UnbDroid/balancer_race/placas/PDFs/invertida_alimentacao_etch_copper_bottom.pdf

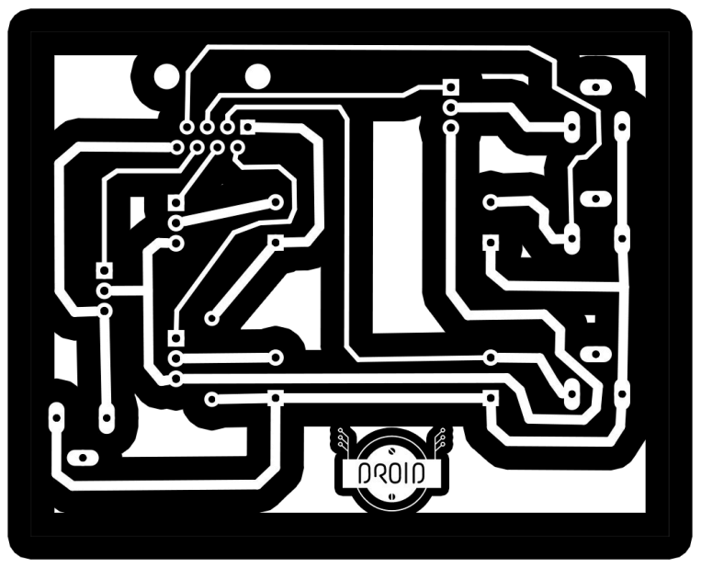
[picture p1: page 1]
