UnbDroid/balancer_race/placas/PDFs/invertida_principal_etch_copper_bottom.pdf

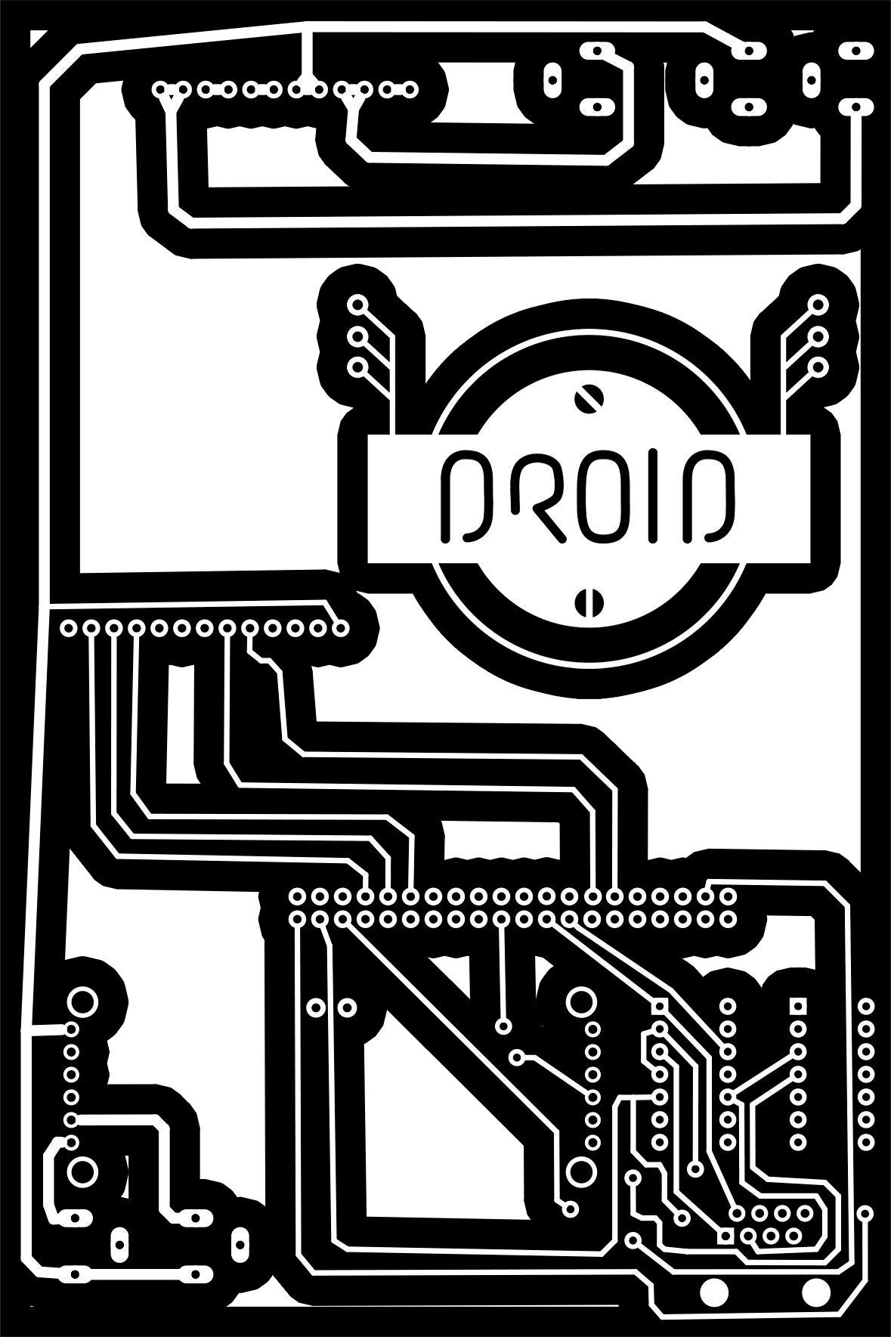
[picture p2: page 1]
