UnbDroid/balancer_race/placas/PDFs/invertida_principal_etch_copper_top.pdf

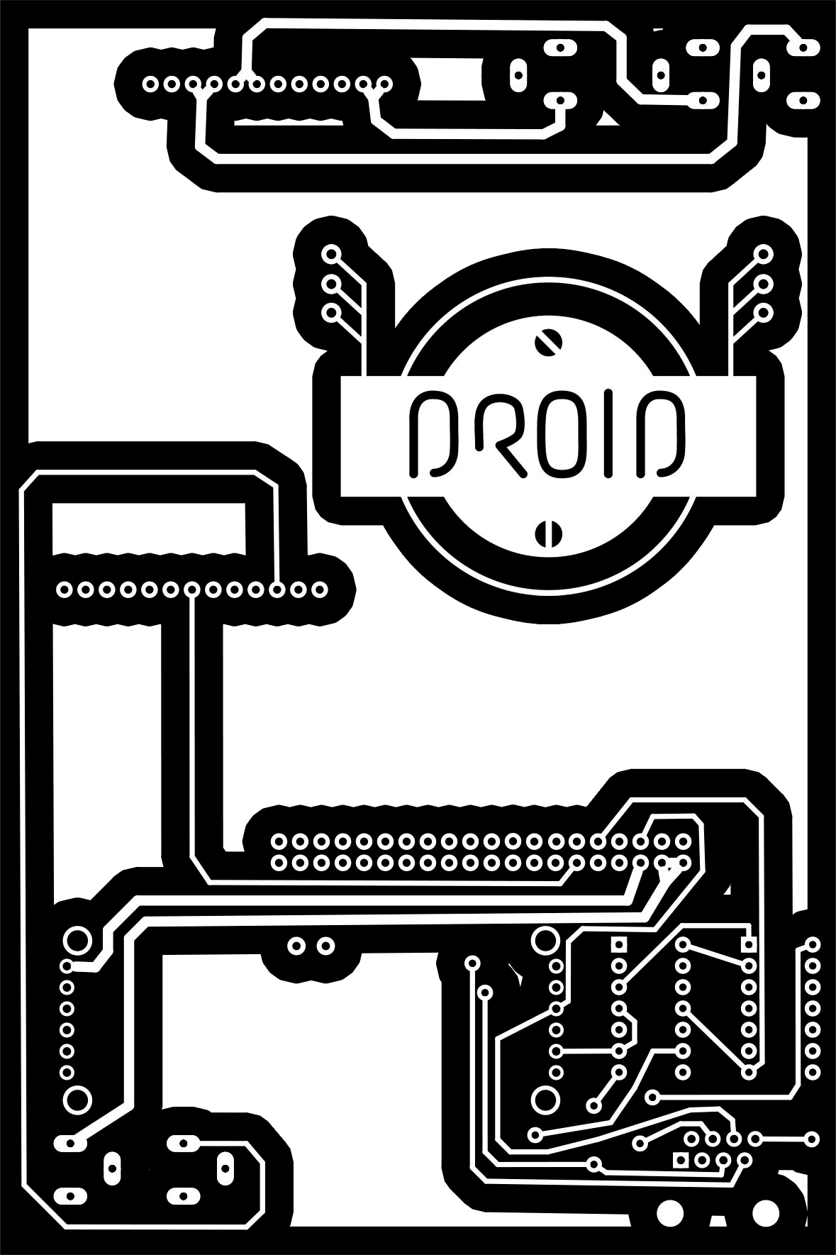
[picture p3: page 1]
