UnbDroid/balancer_race/placas/PDFs/invertidos merge.pdf

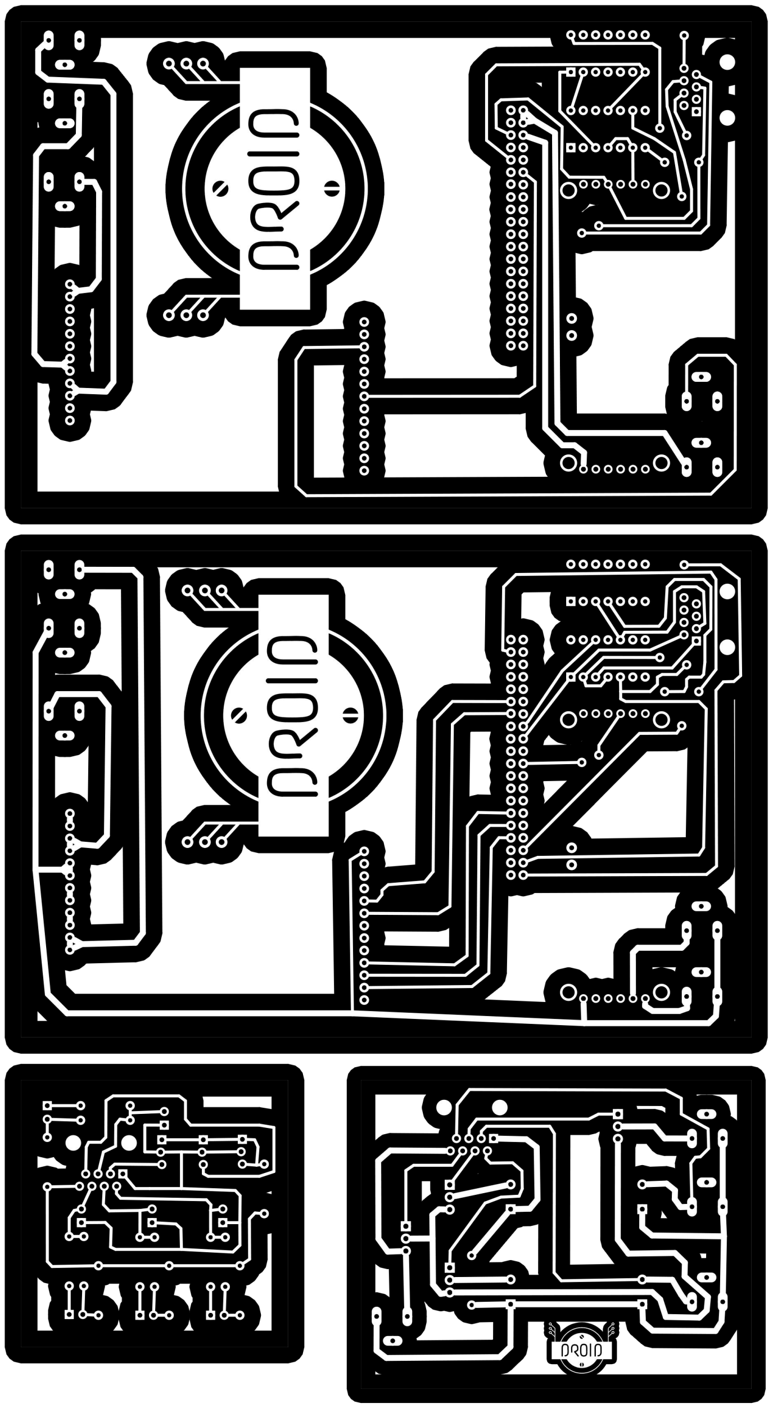
[picture p4: page 1]
