UnbDroid/balancer_race/placas/PDFs/invertida_painel_etch_copper_bottom.pdf

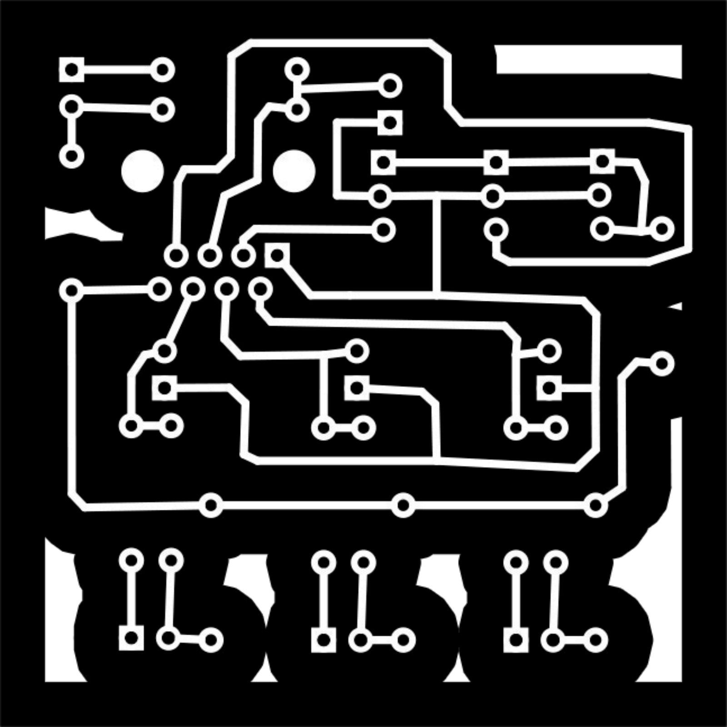
[picture p5: page 1]
