UnbDroid/balancer_race/placas/PDFs/sensores/pronto_para_impressao_sensores_etch_copper_bottom_mirror.pdf

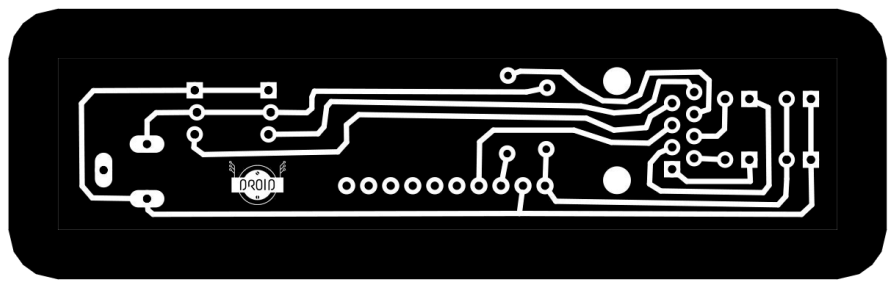
[picture p6: page 1]
