UnbDroid/balancer_race/placas/PDFs/alimentacao2/alimentacao invertida.pdf

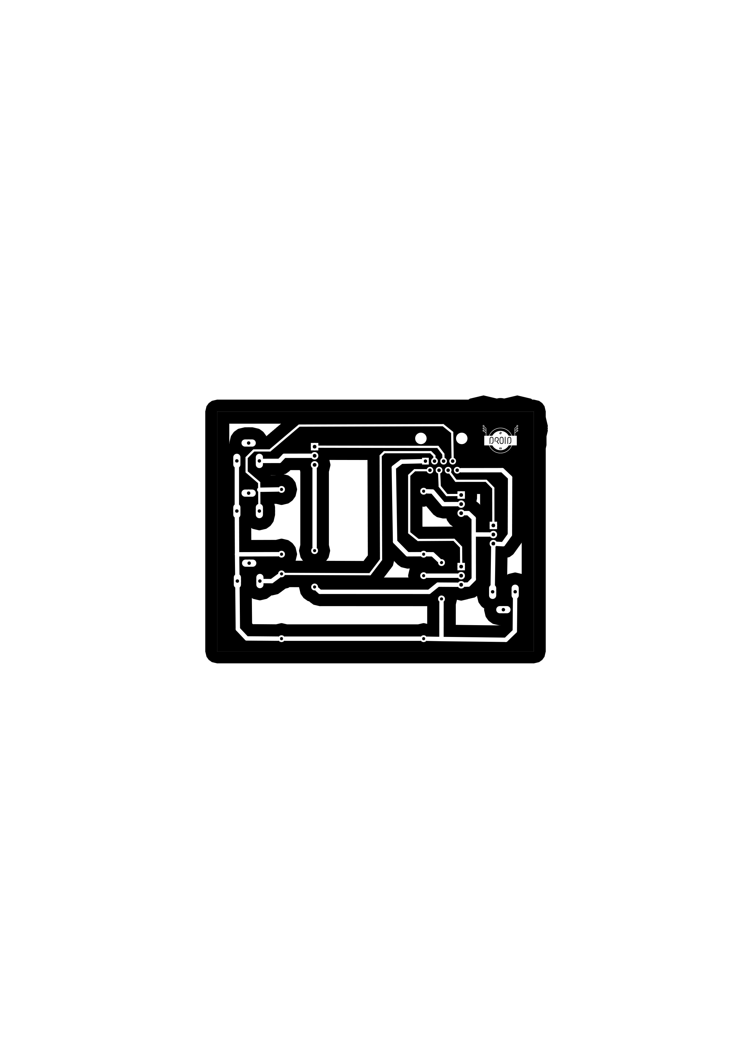
[picture p7: page 1]
