UnbDroid/balancer_race/MATLAB/plots/accel_xyz_static.jpg

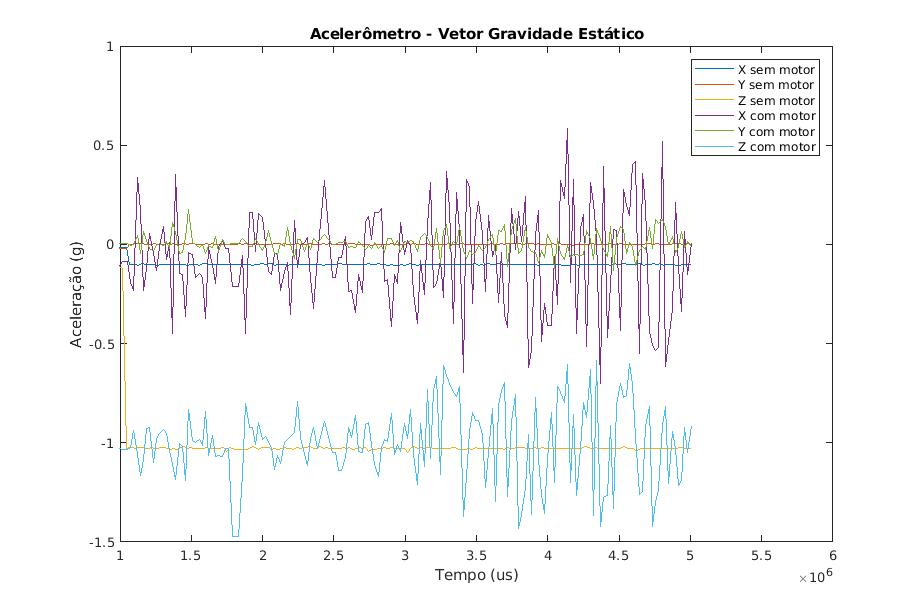
MATLAB/plots/accel_xyz_static.jpg
