UnbDroid/balancer_race/MATLAB/plots/accelXlowfilter.jpg

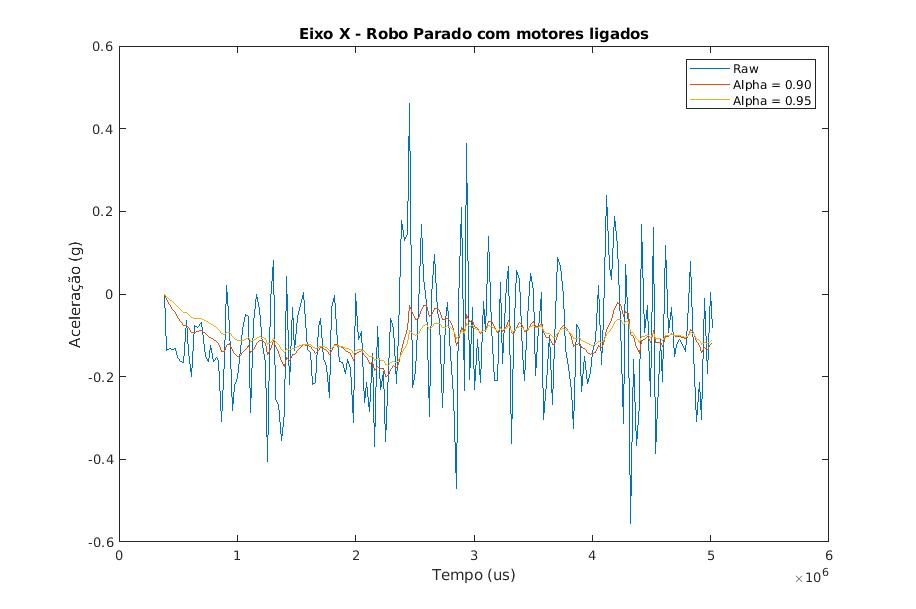
MATLAB/plots/accelXlowfilter.jpg
