UnbDroid/balancer_race/MATLAB/plots/accelYlowfilter.jpg

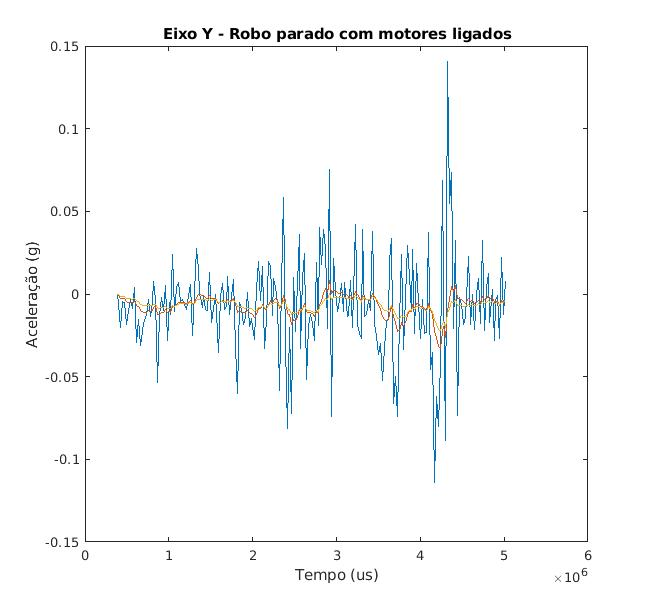
MATLAB/plots/accelYlowfilter.jpg
