UnbDroid/balancer_race/MATLAB/plots/accelZlowfilter.jpg

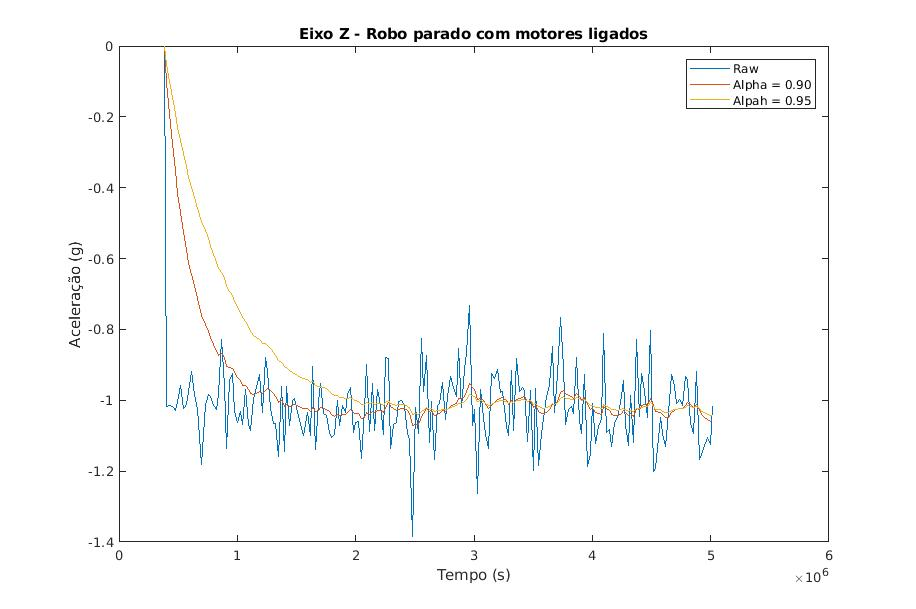
MATLAB/plots/accelZlowfilter.jpg
