UnbDroid/balancer_race/MATLAB/plots/control_gyro_accel_alpha_070.jpg

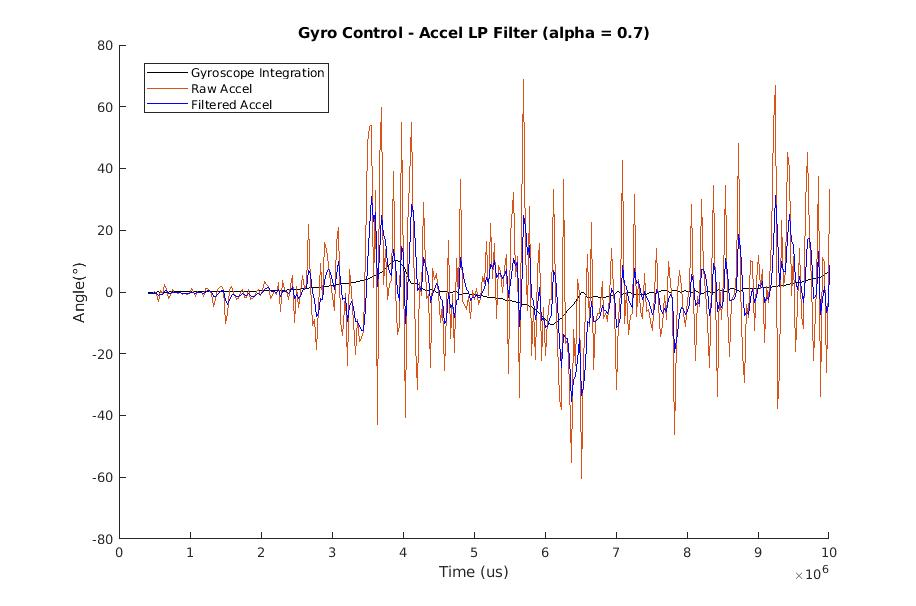
MATLAB/plots/control_gyro_accel_alpha_070.jpg
