UnbDroid/balancer_race/MATLAB/plots/control_gyro_accel_alpha_080.jpg

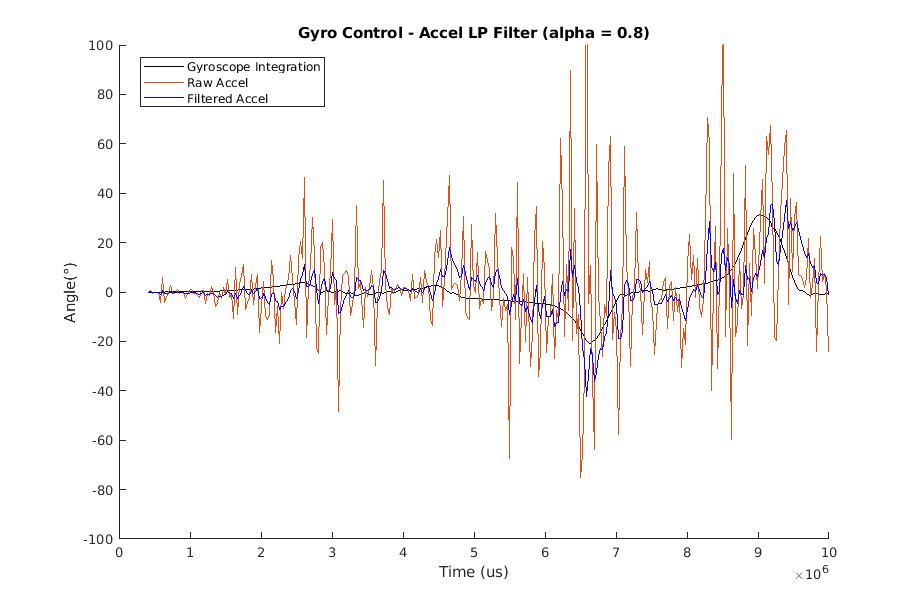
MATLAB/plots/control_gyro_accel_alpha_080.jpg
