UnbDroid/balancer_race/MATLAB/plots/controlandoMotores/endofthedeadzone.jpg

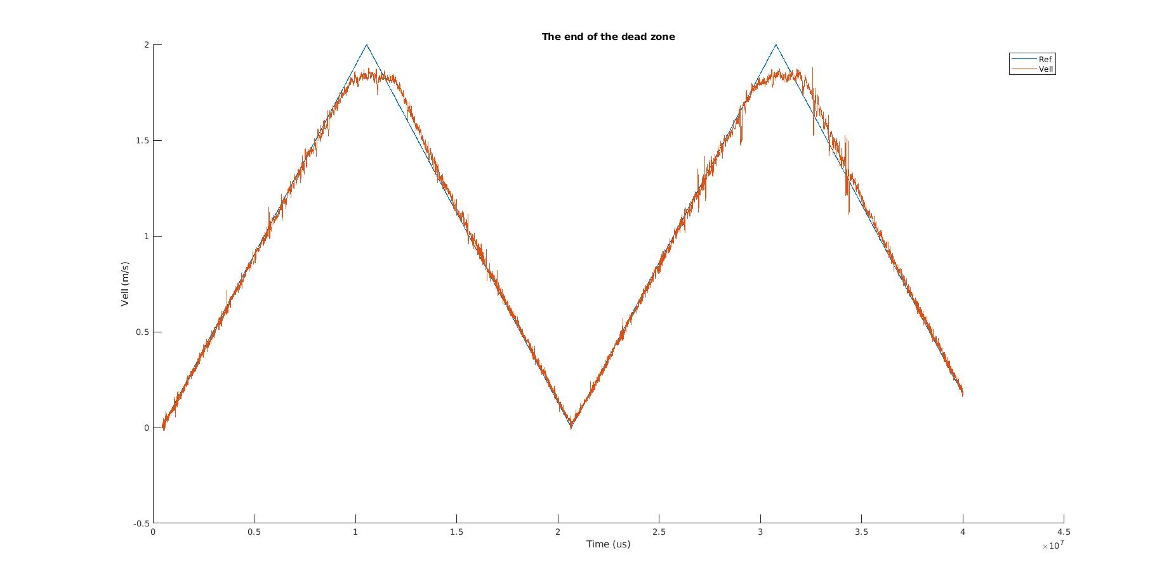
MATLAB/plots/controlandoMotores/endofthedeadzone.jpg
