UnbDroid/balancer_race/MATLAB/plots/controlandoMotores/plot.jpg

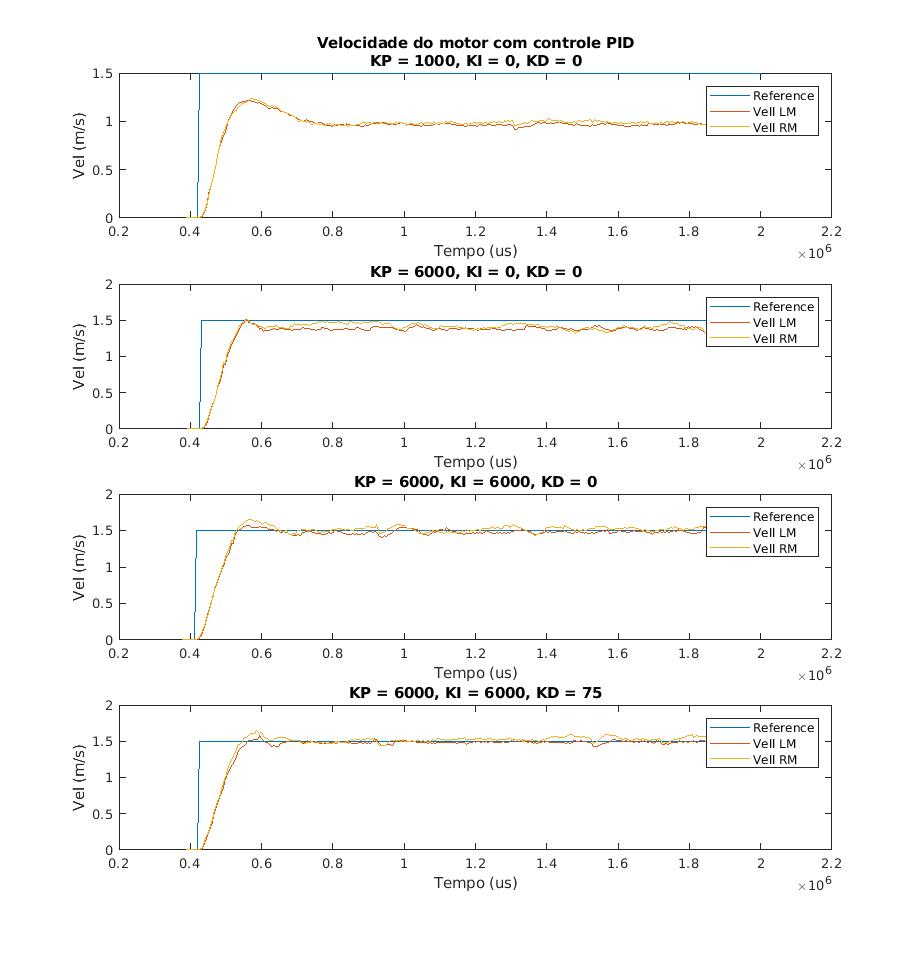
MATLAB/plots/controlandoMotores/plot.jpg
