UnbDroid/balancer_race/MATLAB/plots/filtrandoEncoder/fast.jpg

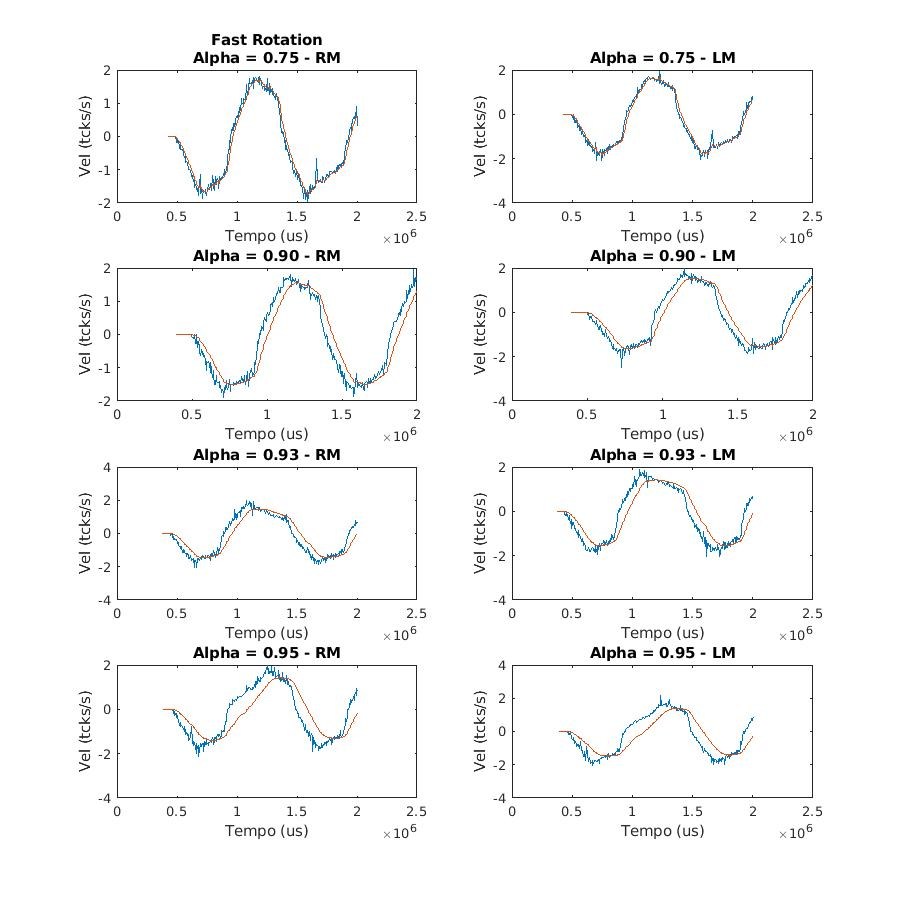
MATLAB/plots/filtrandoEncoder/fast.jpg
