UnbDroid/balancer_race/MATLAB/plots/filtrandoEncoder/slow.jpg

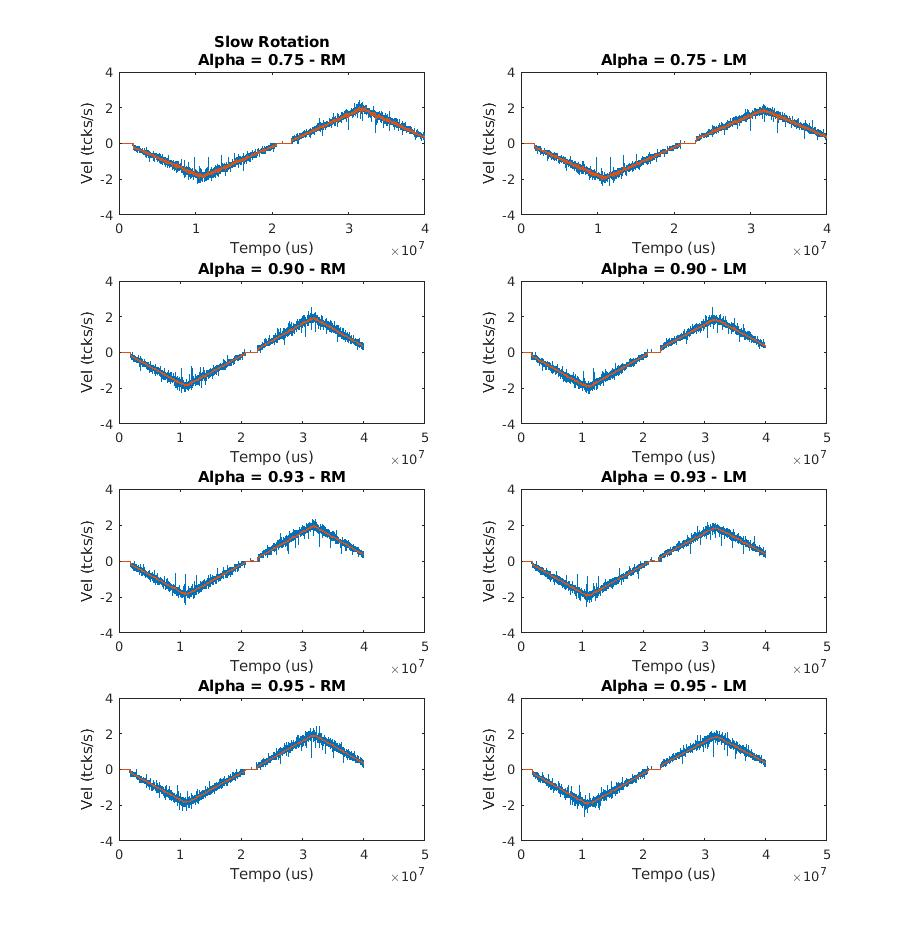
MATLAB/plots/filtrandoEncoder/slow.jpg
