UnbDroid/balancer_race/MATLAB/plots/ligandoeconder/offmottoroffecoder.jpg

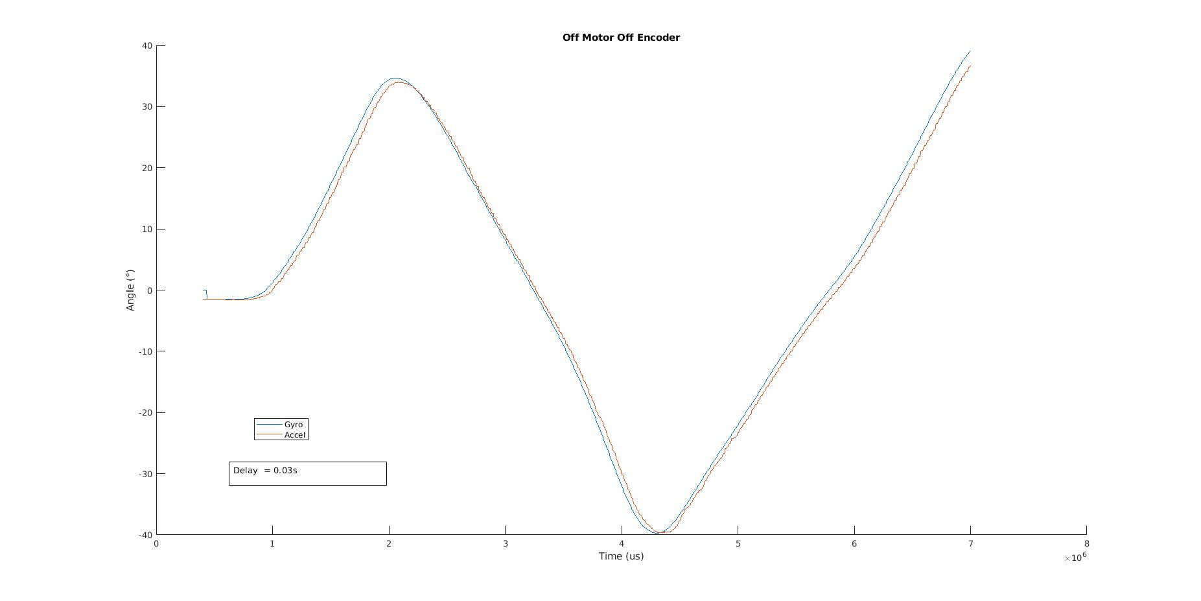
MATLAB/plots/ligandoeconder/offmottoroffecoder.jpg
