UnbDroid/balancer_race/MATLAB/plots/ligandoeconder/onmottoroffecoder.jpg

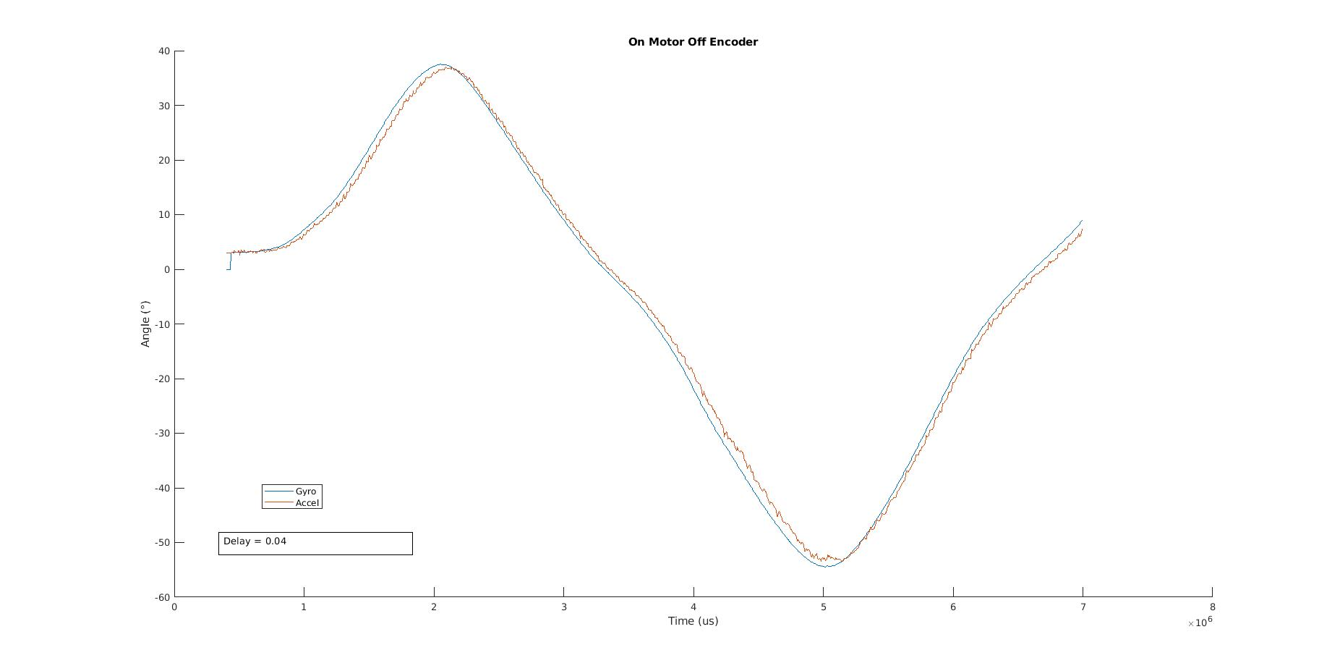
MATLAB/plots/ligandoeconder/onmottoroffecoder.jpg
