UnbDroid/balancer_race/MATLAB/plots/ligandoeconder/onmottoronecoder.jpg

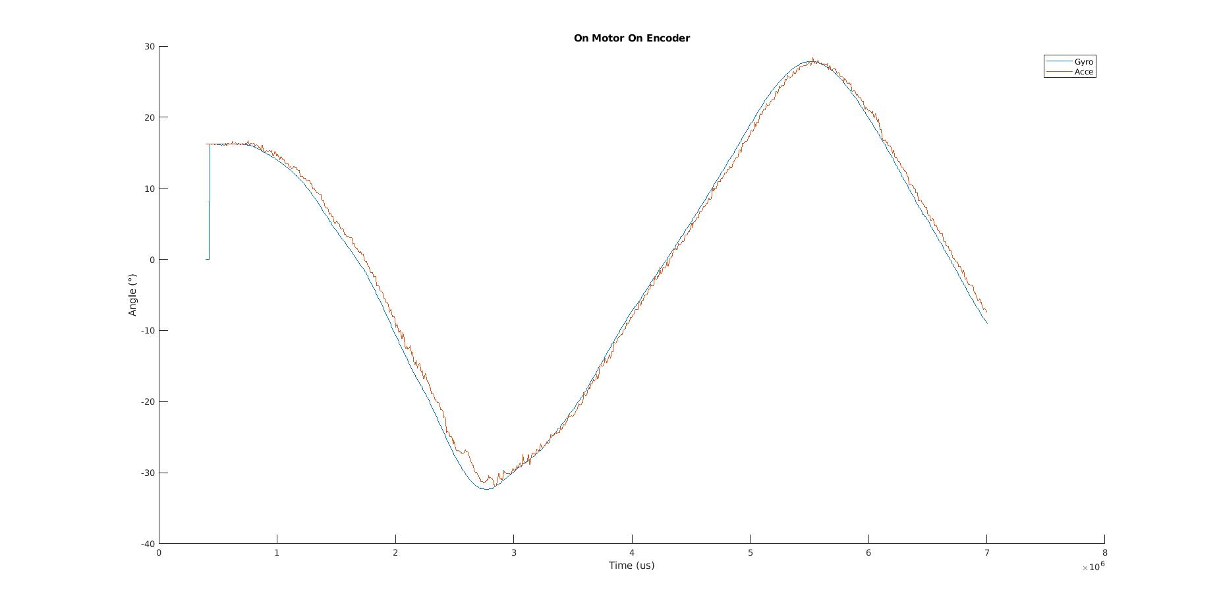
MATLAB/plots/ligandoeconder/onmottoronecoder.jpg
