UnbDroid/balancer_race/MATLAB/plots/motor_rapido/equilibrando.jpg

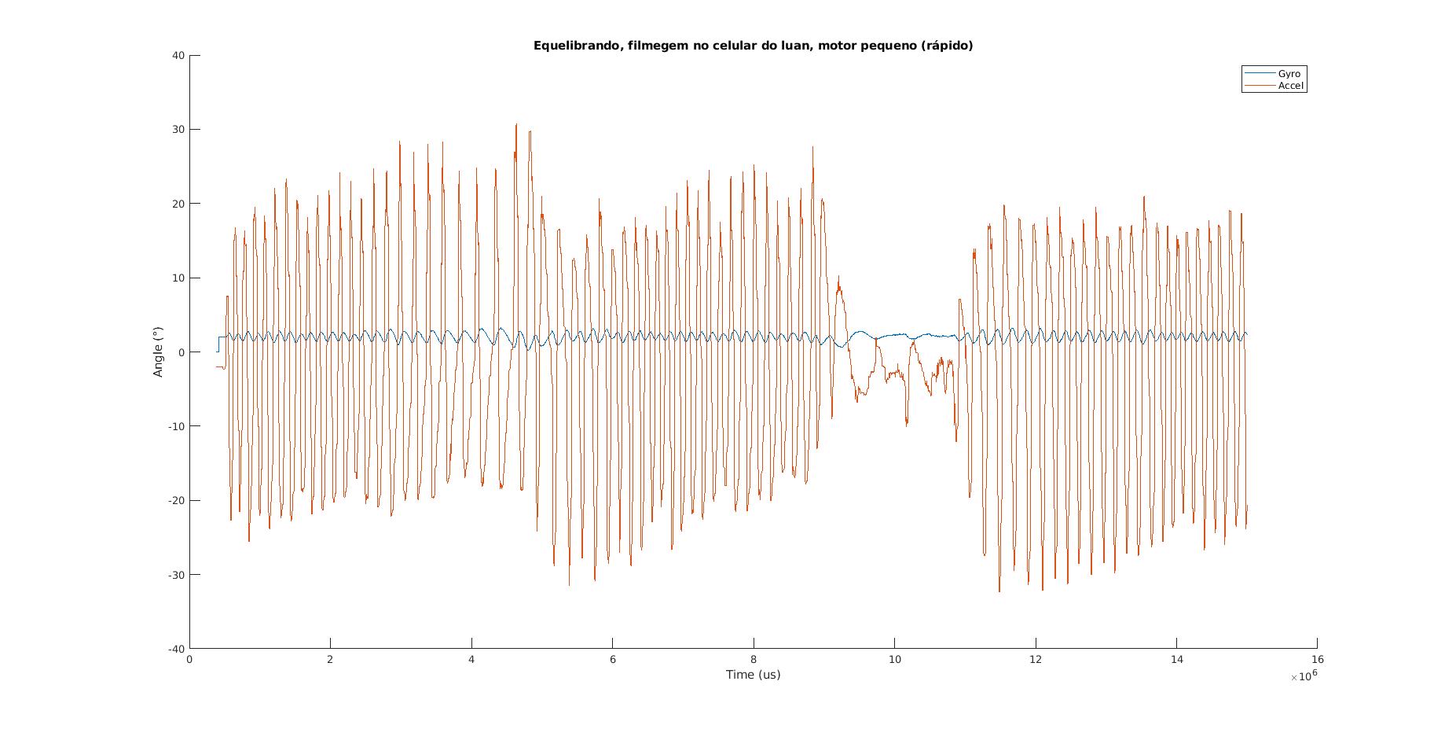
MATLAB/plots/motor_rapido/equilibrando.jpg
