UnbDroid/balancer_race/MATLAB/plots/motor_rapido/offmotor_offencoder.jpg

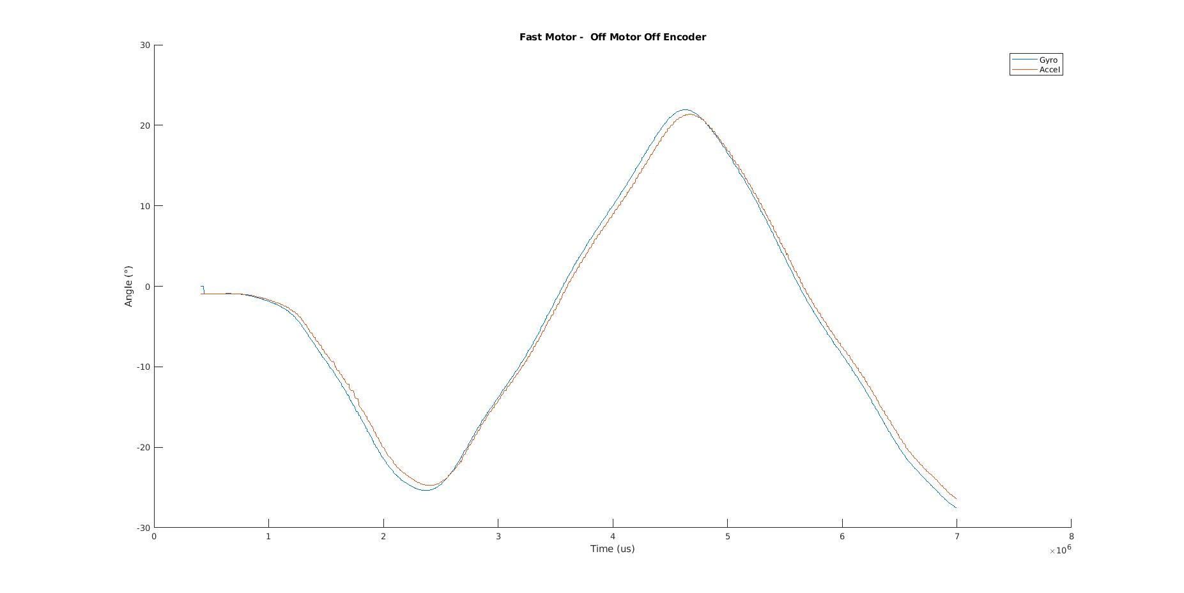
MATLAB/plots/motor_rapido/offmotor_offencoder.jpg
