UnbDroid/balancer_race/MATLAB/plots/motor_rapido/onmotor_offencoder.jpg

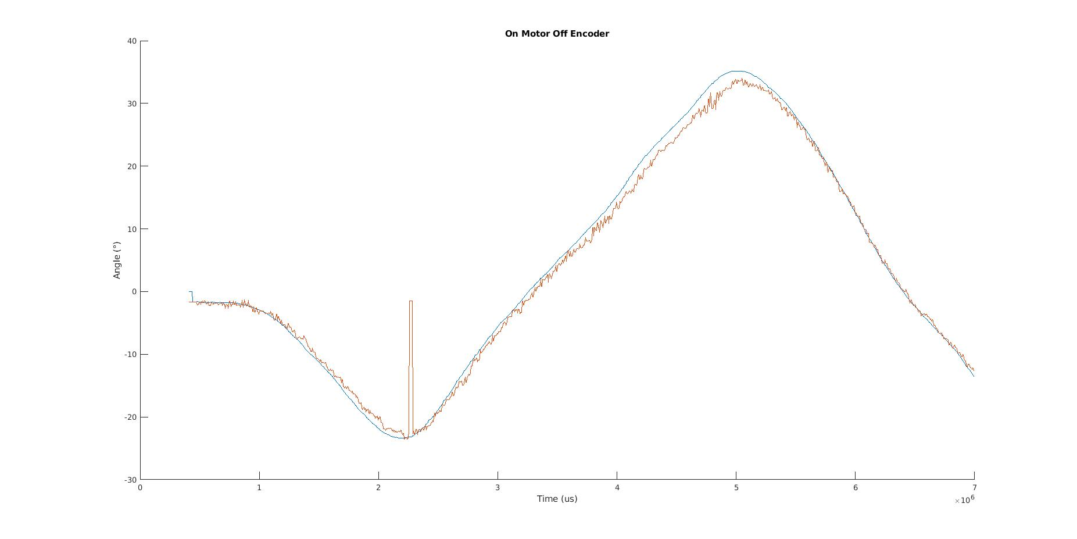
MATLAB/plots/motor_rapido/onmotor_offencoder.jpg
