UnbDroid/balancer_race/MATLAB/plots/motor_rapido/onmotor_onencoder.jpg

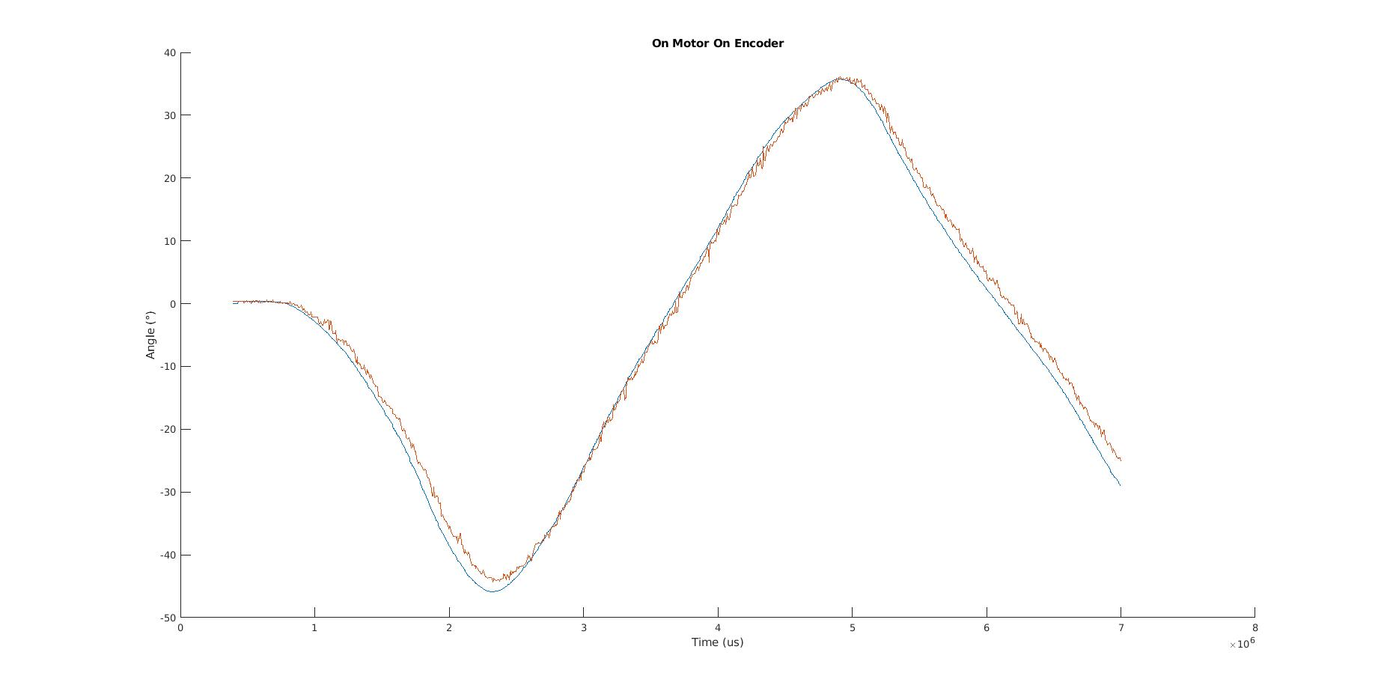
MATLAB/plots/motor_rapido/onmotor_onencoder.jpg
