UnbDroid/balancer_race/MATLAB/plots/mvmda_lowpass/n3a00-offmotor.jpg

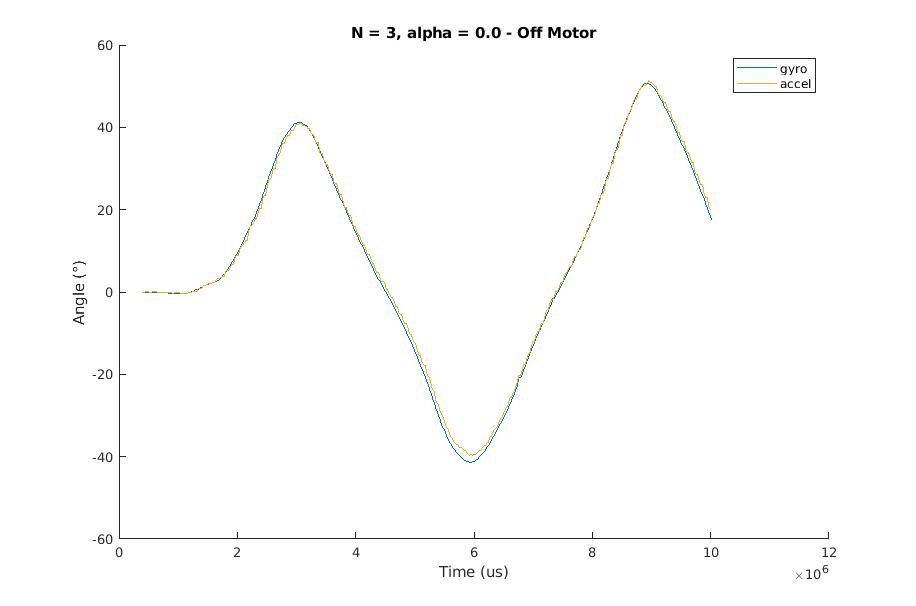
MATLAB/plots/mvmda_lowpass/n3a00-offmotor.jpg
