UnbDroid/balancer_race/MATLAB/plots/mvmda_lowpass/n3a03-offmotor.jpg

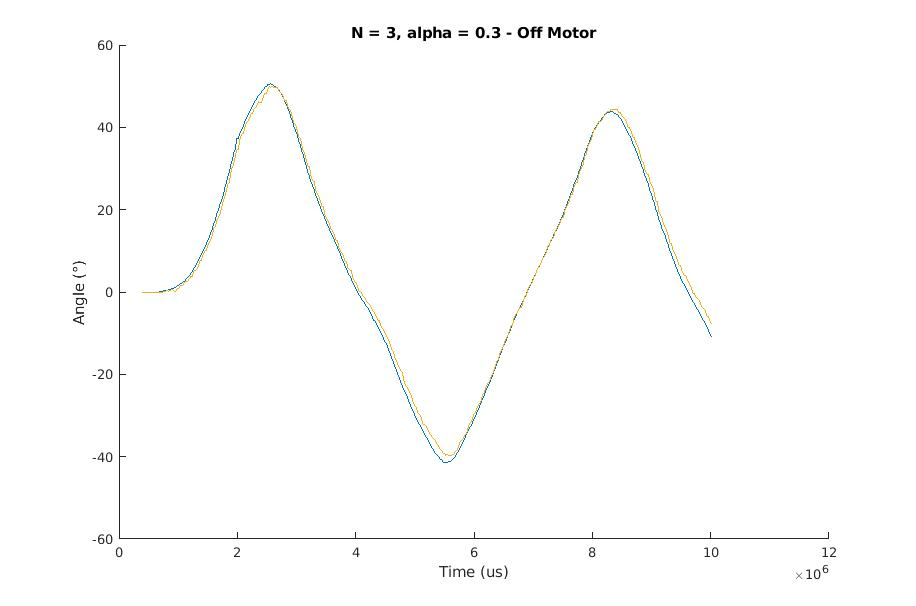
MATLAB/plots/mvmda_lowpass/n3a03-offmotor.jpg
