UnbDroid/balancer_race/MATLAB/plots/mvmda_lowpass/n3a03-onmotor.jpg

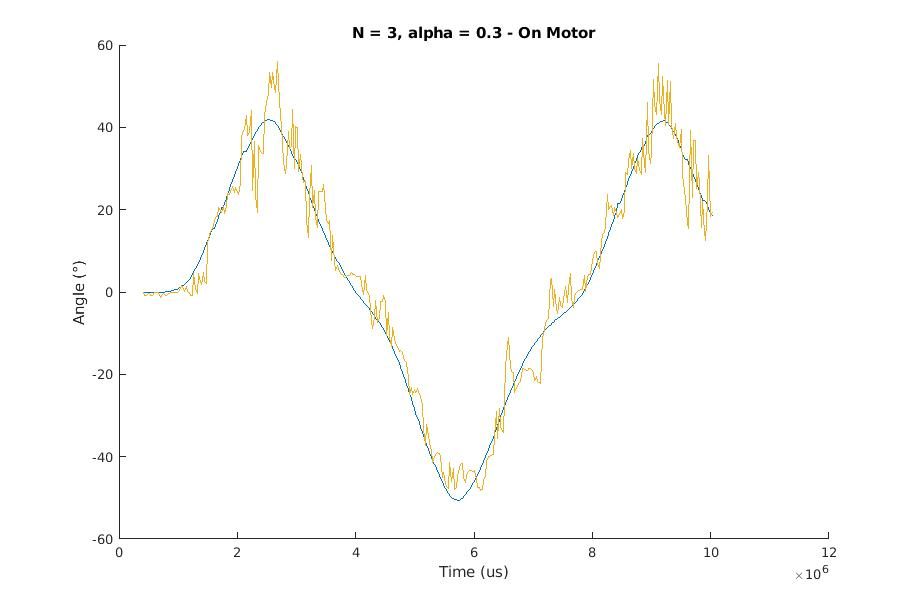
MATLAB/plots/mvmda_lowpass/n3a03-onmotor.jpg
