UnbDroid/balancer_race/MATLAB/plots/mvmda_lowpass/n3a05-offmotor.jpg

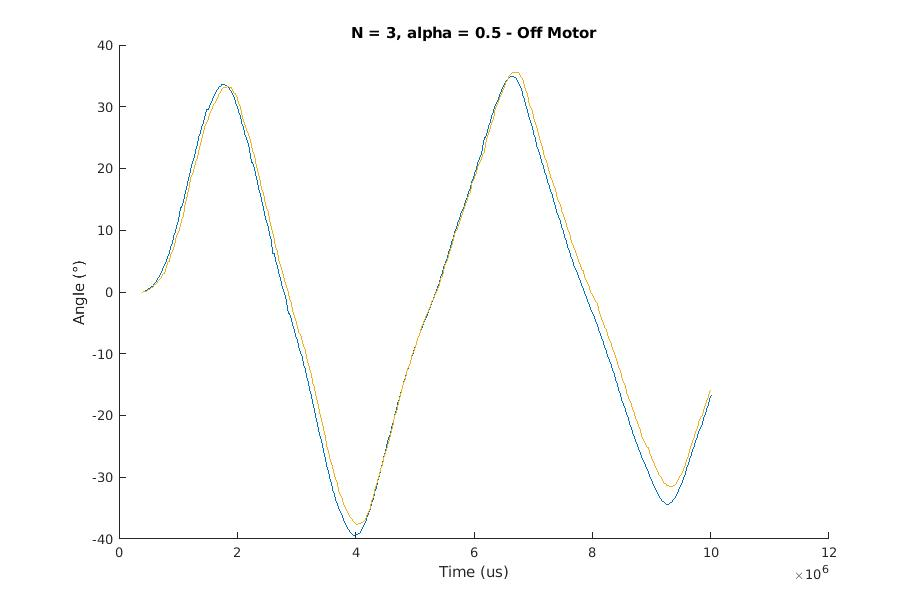
MATLAB/plots/mvmda_lowpass/n3a05-offmotor.jpg
