UnbDroid/balancer_race/MATLAB/plots/mvmda_lowpass/n3a07-offmotor.jpg

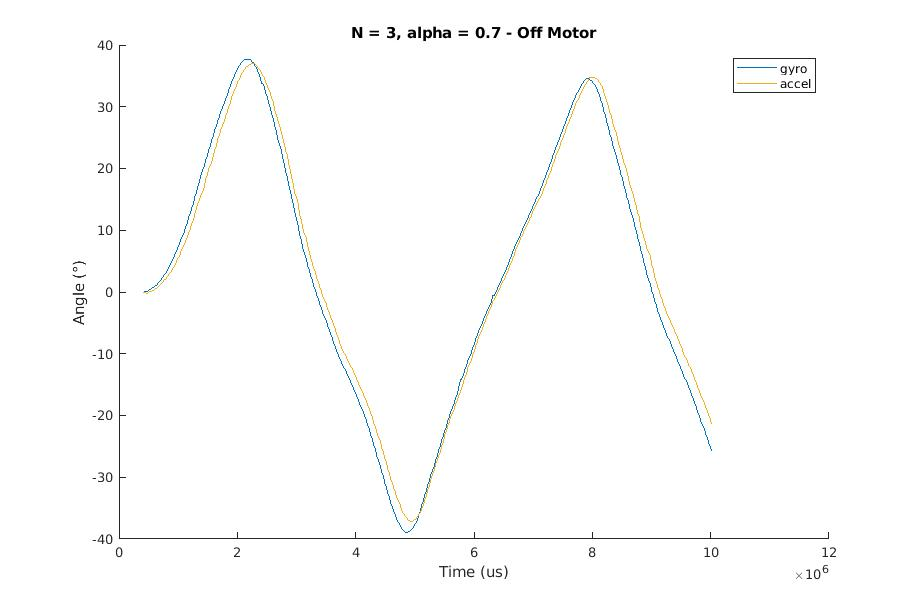
MATLAB/plots/mvmda_lowpass/n3a07-offmotor.jpg
