UnbDroid/balancer_race/MATLAB/plots/mvmda_lowpass/n3a07-onmotor.jpg

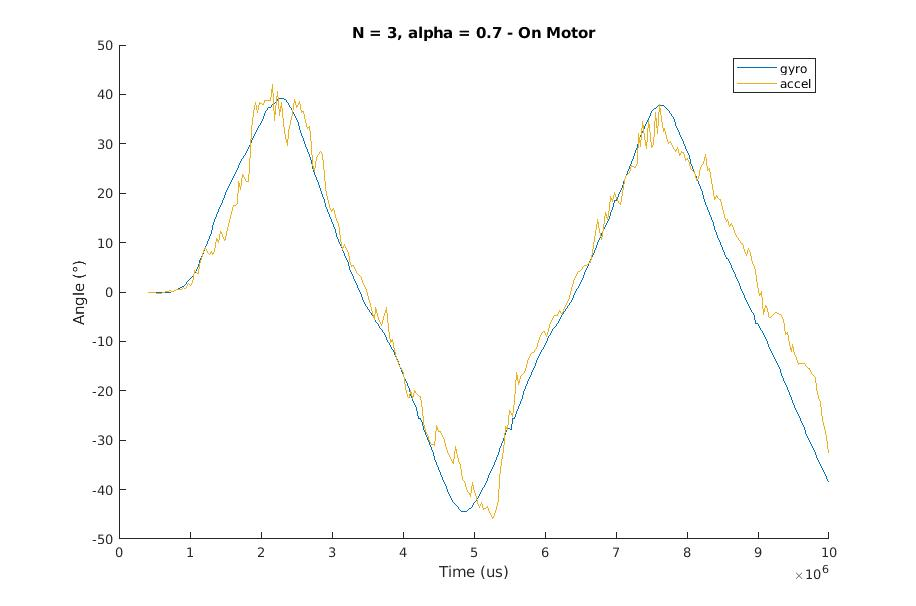
MATLAB/plots/mvmda_lowpass/n3a07-onmotor.jpg
