UnbDroid/balancer_race/MATLAB/plots/mvmda_lowpass/nofilter-offmotor.jpg

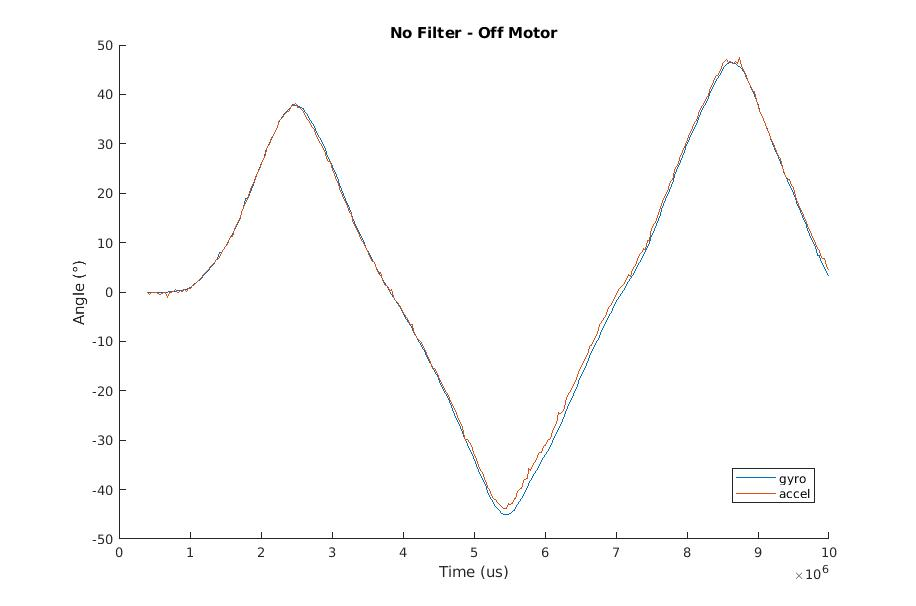
MATLAB/plots/mvmda_lowpass/nofilter-offmotor.jpg
