UnbDroid/balancer_race/MATLAB/plots/mvmda_lowpass/nofilter-onmotor.jpg

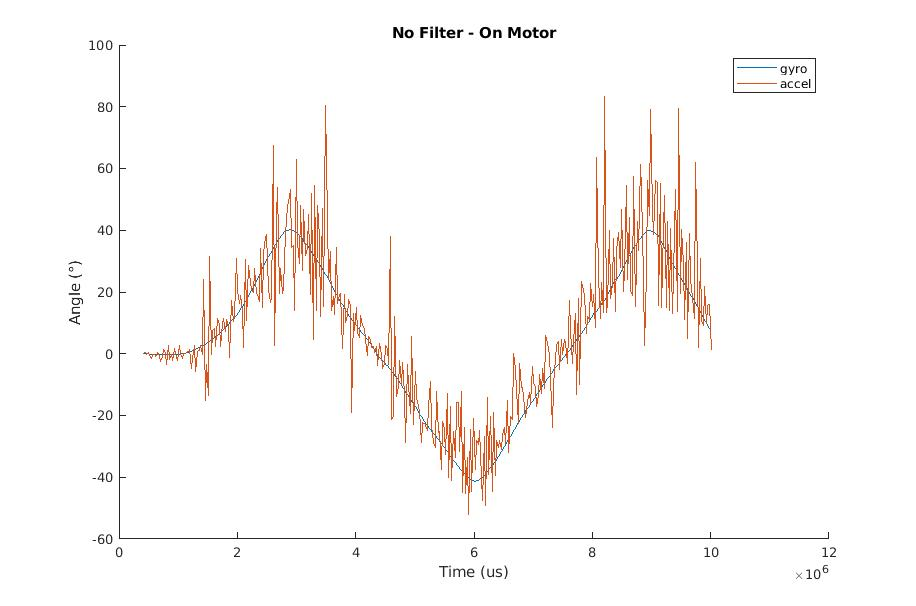
MATLAB/plots/mvmda_lowpass/nofilter-onmotor.jpg
