UnbDroid/balancer_race/MATLAB/plots/EncoderTest/controle/18h30.jpg

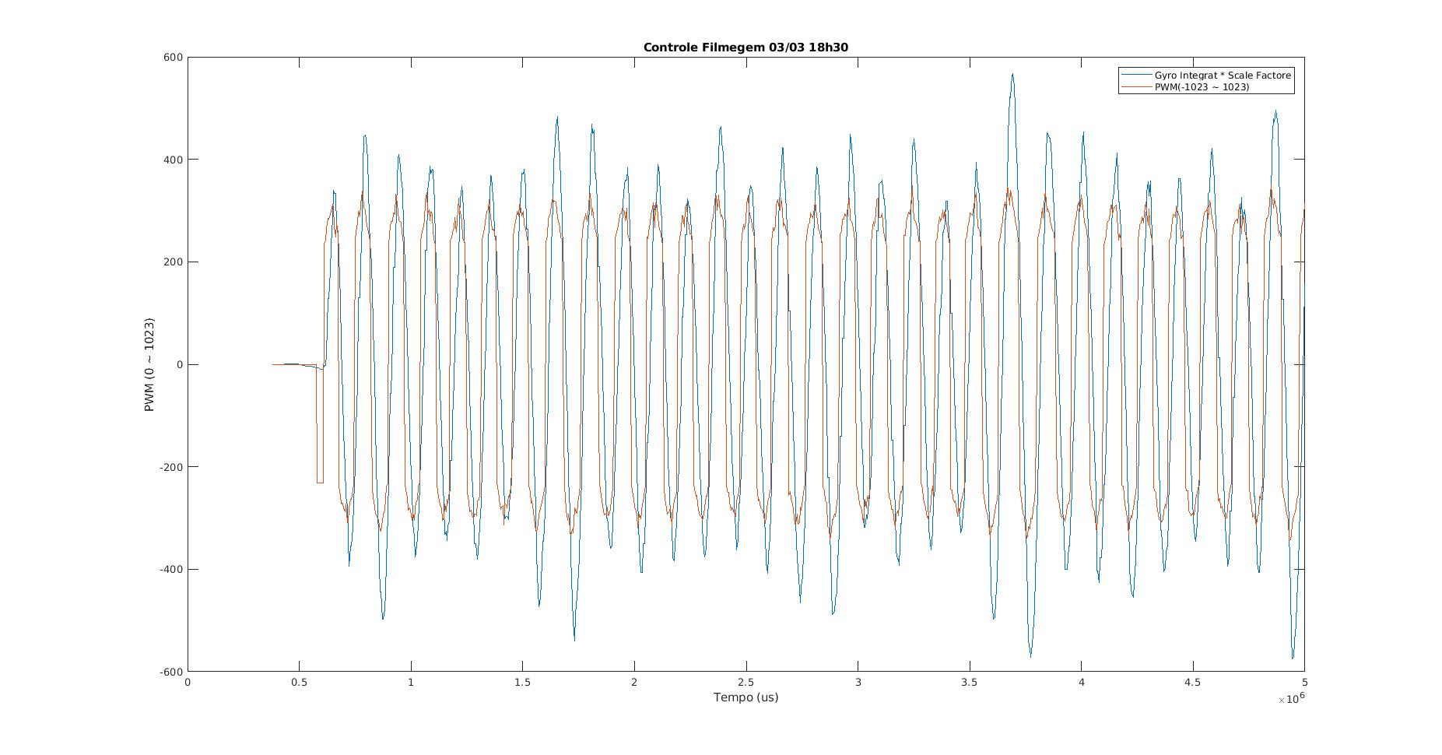
MATLAB/plots/EncoderTest/controle/18h30.jpg
