UnbDroid/balancer_race/MATLAB/plots/EncoderTest/dead_zone/Left Motor - OnFwd - DZ.jpg

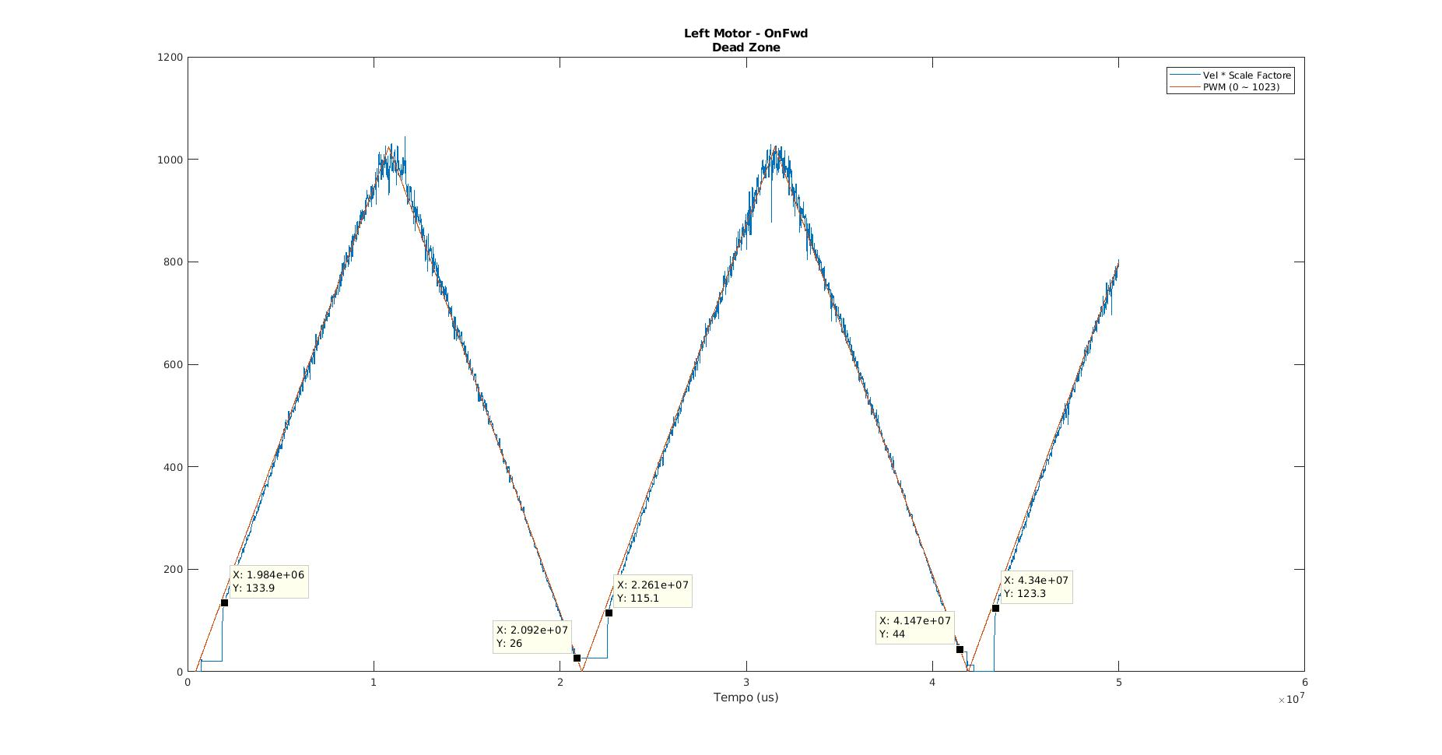
MATLAB/plots/EncoderTest/dead_zone/Left Motor - OnFwd - DZ.jpg
