UnbDroid/balancer_race/MATLAB/plots/EncoderTest/dead_zone/Left Motor - OnFwd - Raw.jpg

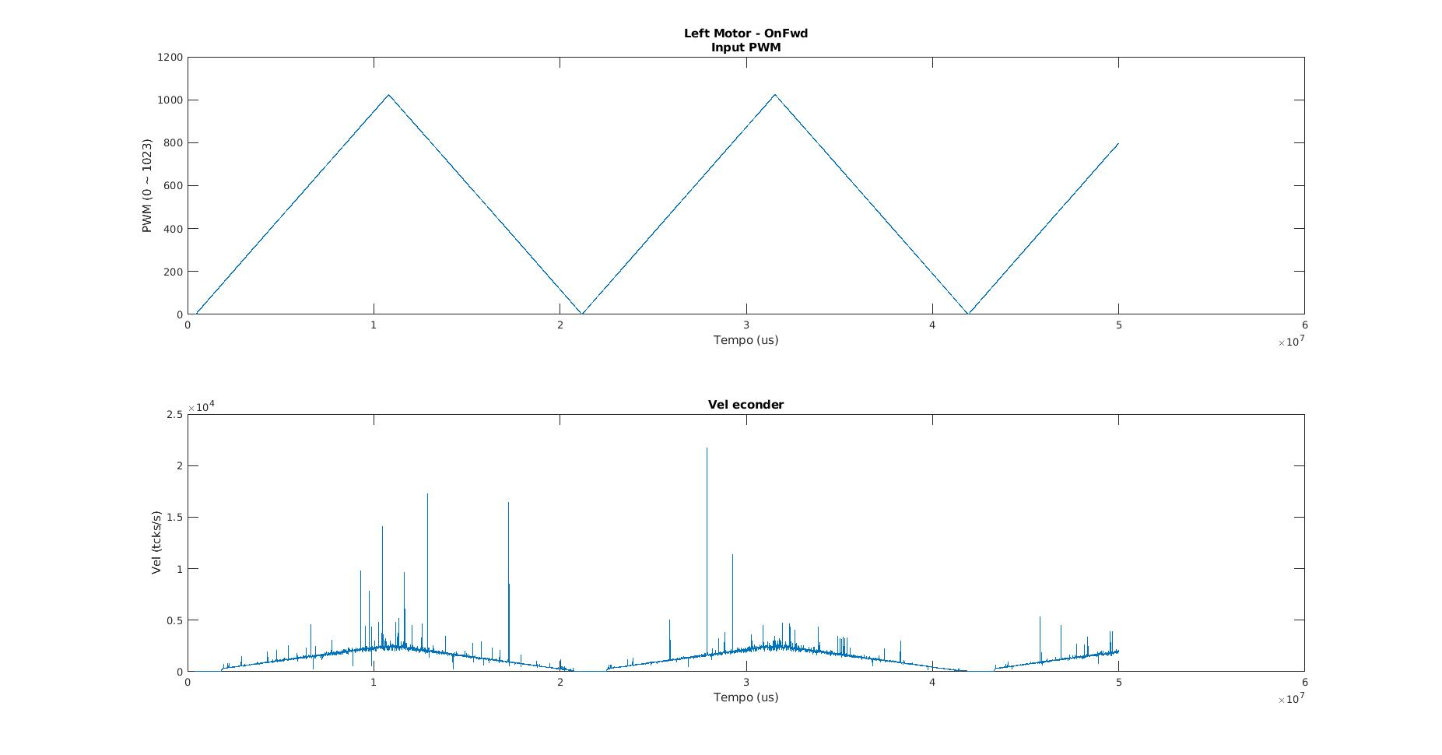
MATLAB/plots/EncoderTest/dead_zone/Left Motor - OnFwd - Raw.jpg
