UnbDroid/balancer_race/MATLAB/plots/EncoderTest/dead_zone/Right Motor - OnFwd - Raw.jpg

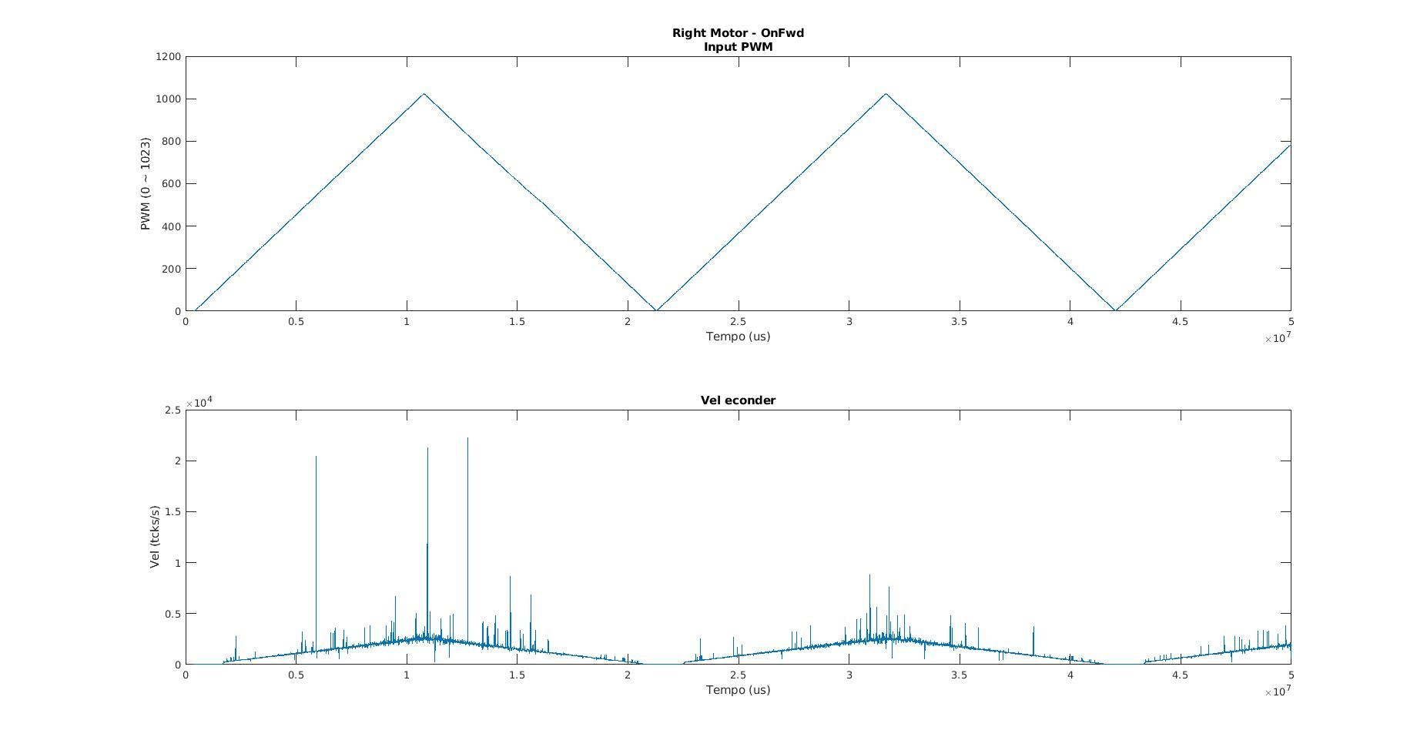
MATLAB/plots/EncoderTest/dead_zone/Right Motor - OnFwd - Raw.jpg
