UnbDroid/balancer_race/MATLAB/plots/EncoderTest/dead_zone/Right Motor - OnFwd - tratamento.jpg

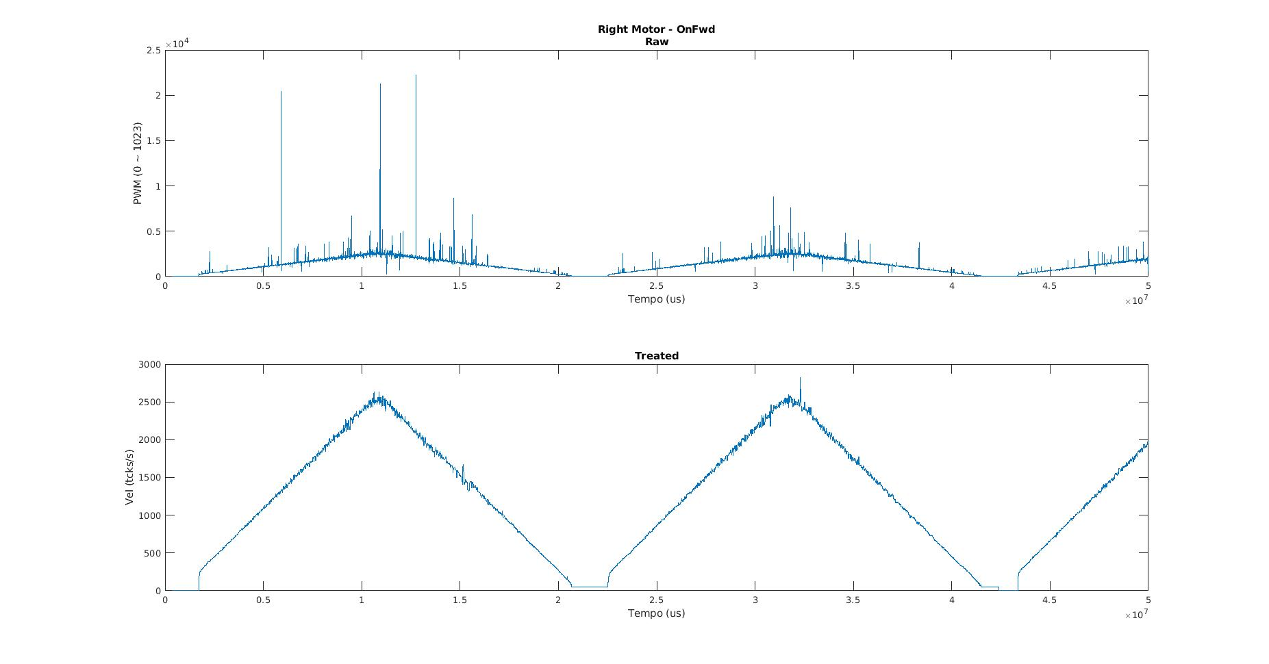
MATLAB/plots/EncoderTest/dead_zone/Right Motor - OnFwd - tratamento.jpg
