UnbDroid/balancer_race/MATLAB/plots/EncoderTest/dead_zone/Right Motor - OnRev - tratamento.jpg

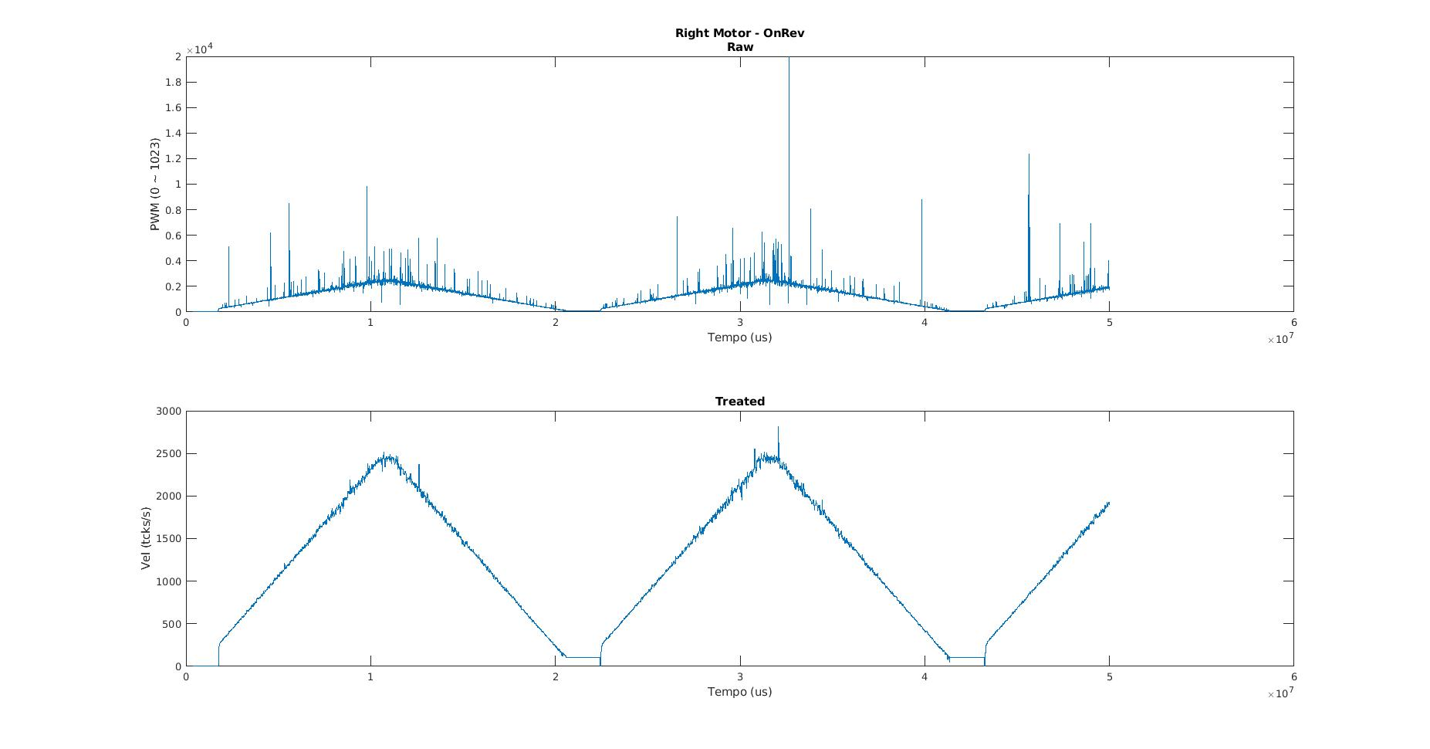
MATLAB/plots/EncoderTest/dead_zone/Right Motor - OnRev - tratamento.jpg
