UnbDroid/balancer_race/MATLAB/plots/accel_pitch_offmotor_static_00022326.pdf

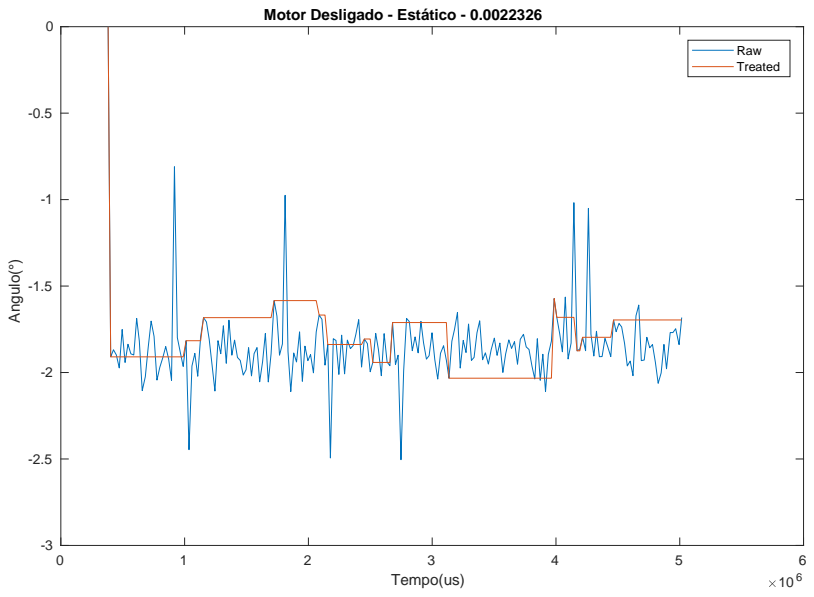
[picture p56: page 1]
Tempo(us); Angulo(°); Raw Treated

Motor Desligado - Estático - 0.0022326
