UnbDroid/balancer_race/MATLAB/plots/accel_pitch_offmotor_static_0011163.pdf

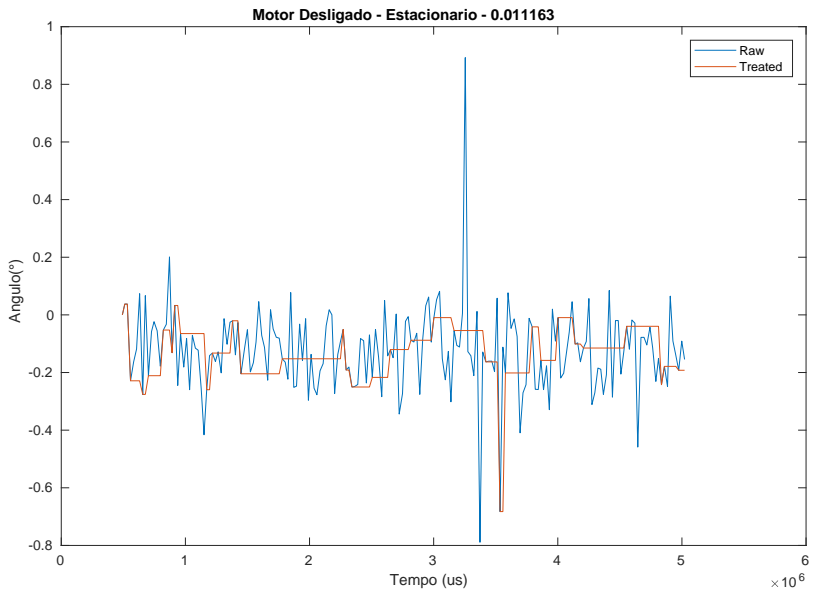
[picture p57: page 1]
Tempo (us); Angulo(°); Raw Treated

Motor Desligado - Estacionario - 0.011163
