UnbDroid/balancer_race/MATLAB/plots/accel_pitch_onmotor_moving_00022326.pdf

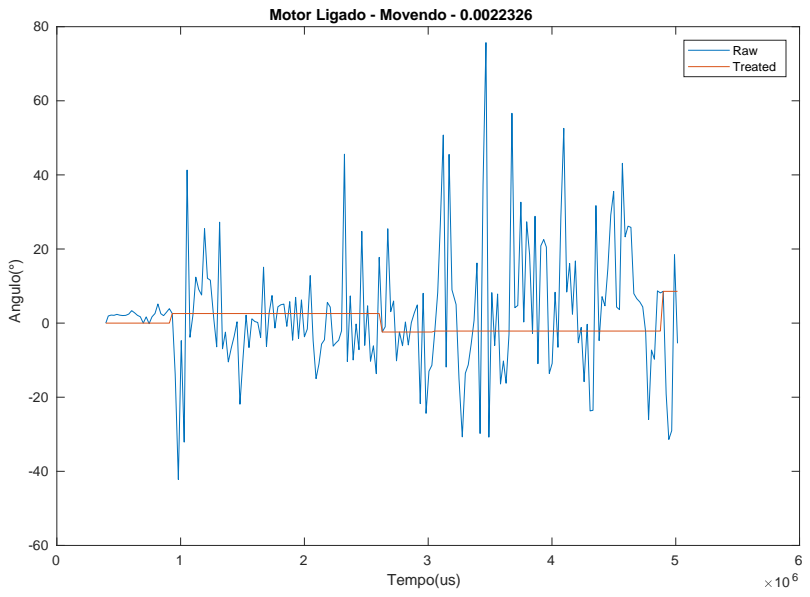
[picture p58: page 1]
Tempo(us); Angulo(°); Raw Treated

Motor Ligado - Movendo - 0.0022326
