UnbDroid/balancer_race/MATLAB/plots/accel_pitch_onmotor_moving_0011163.pdf

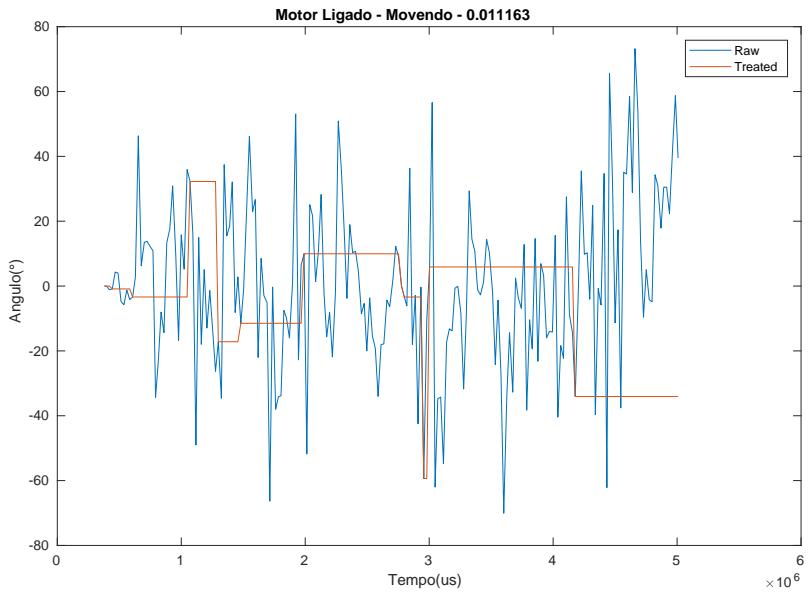
[picture p59: page 1]
Tempo(us); Angulo(°); Raw Treated

Motor Ligado - Movendo - 0.011163
