UnbDroid/balancer_race/MATLAB/plots/accel_pitch_onmotor_static_00022326.pdf

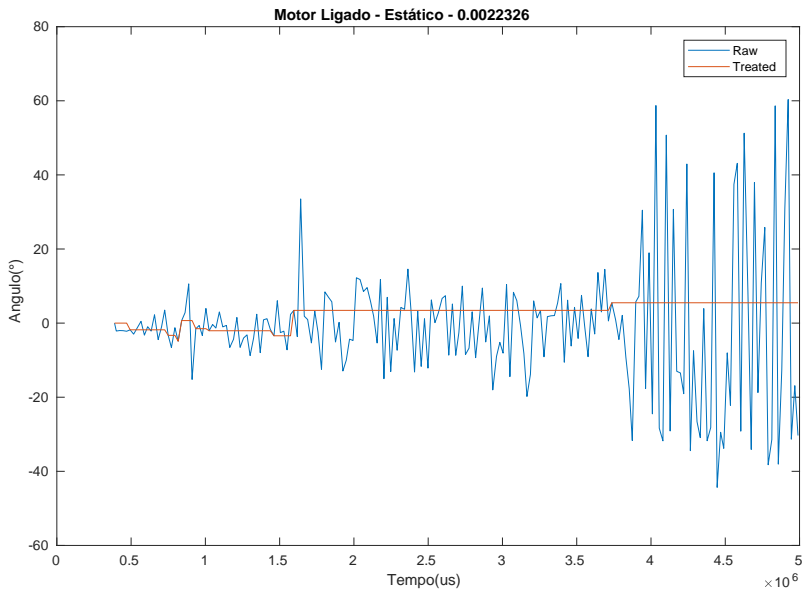
[picture p60: page 1]
Tempo(us); Angulo(°); Raw Treated

Motor Ligado - Estático - 0.0022326
