UnbDroid/balancer_race/MATLAB/plots/accel_pitch_onmotor_static_0011163.pdf

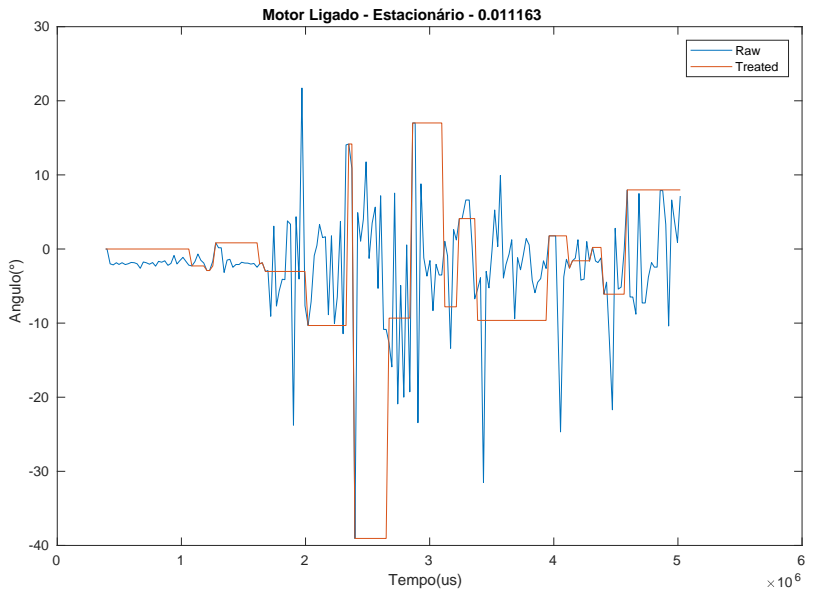
[picture p61: page 1]
Tempo(us); Angulo(°); Raw Treated

Motor Ligado - Estacionário - 0.011163
