UnbDroid/balancer_race/placas/PDFs/principal_etch_copper_bottom.pdf

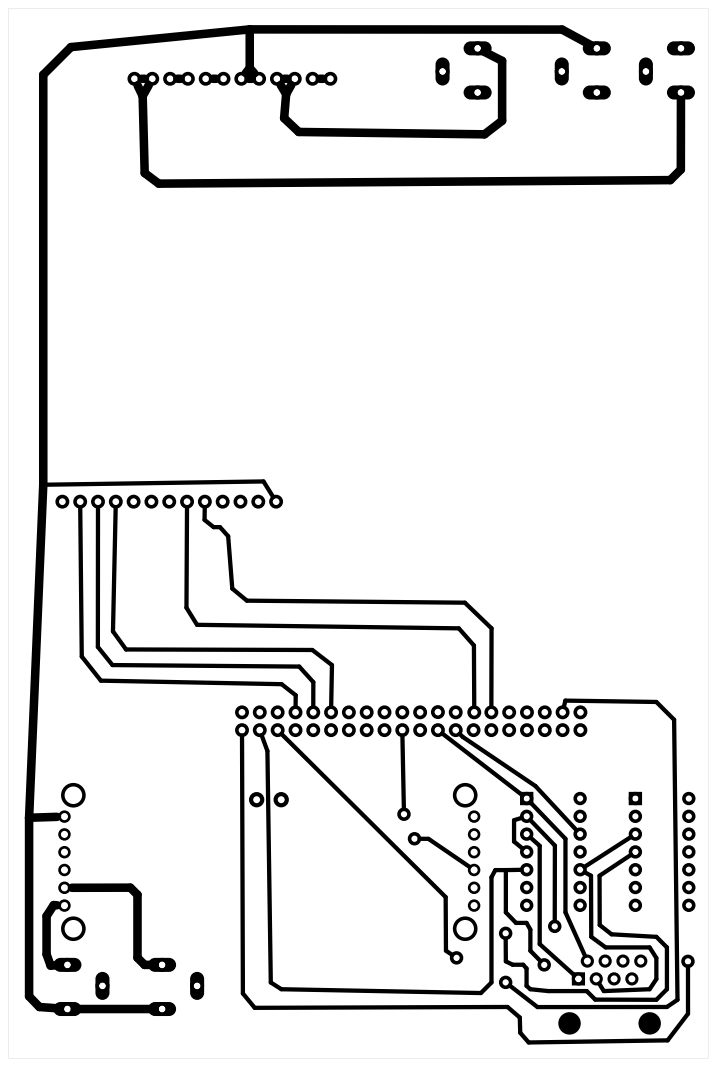
[picture p63: page 1]
