UnbDroid/balancer_race/placas/PDFs/principal_etch_copper_top.pdf

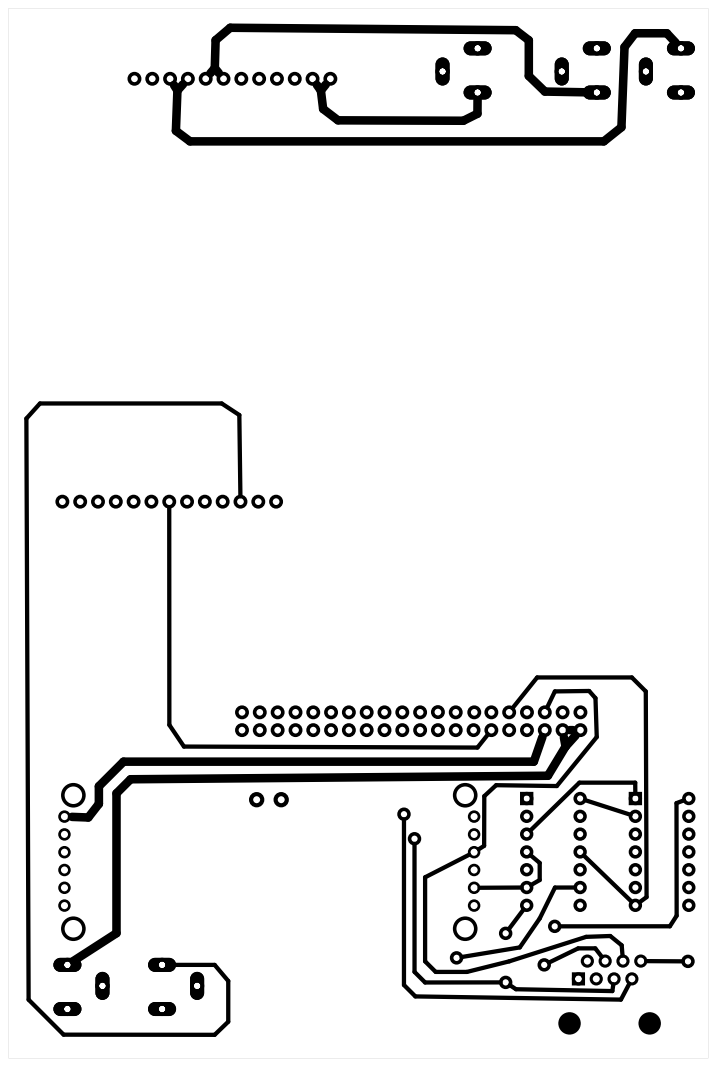
[picture p64: page 1]
