UnbDroid/balancer_race/placas/PDFs/alimentacao_etch_copper_bottom.pdf

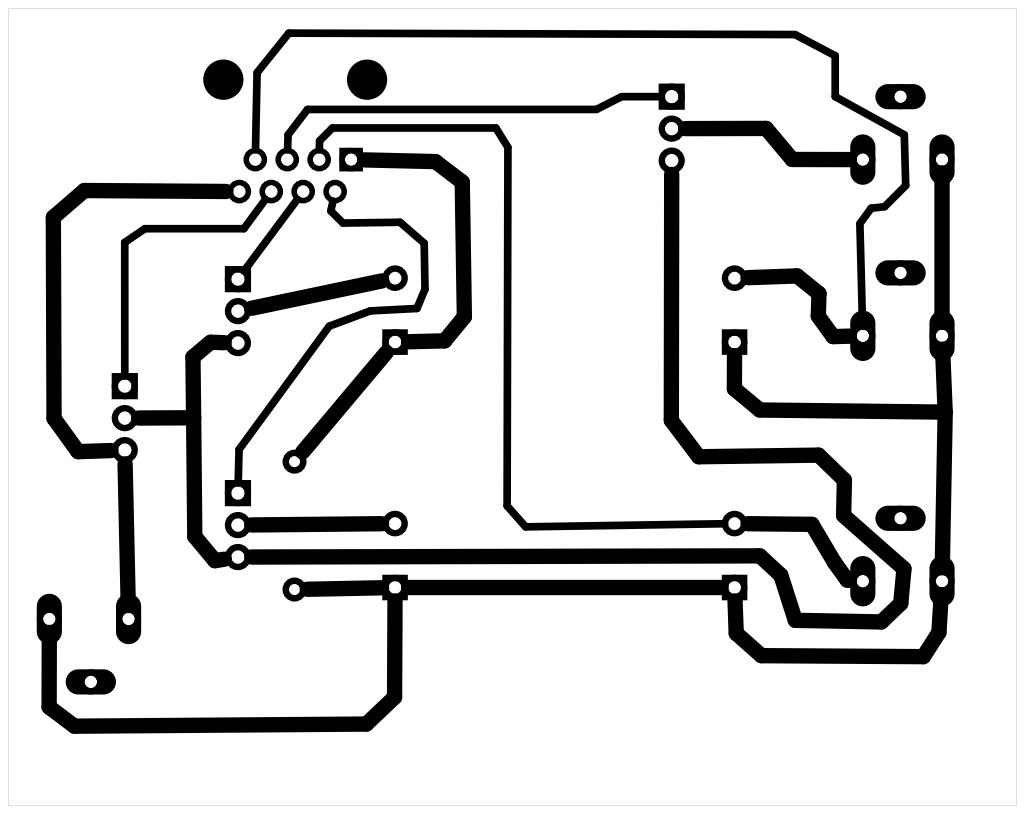
[picture p65: page 1]
