UnbDroid/balancer_race/placas/PDFs/painel_etch_copper_bottom.pdf

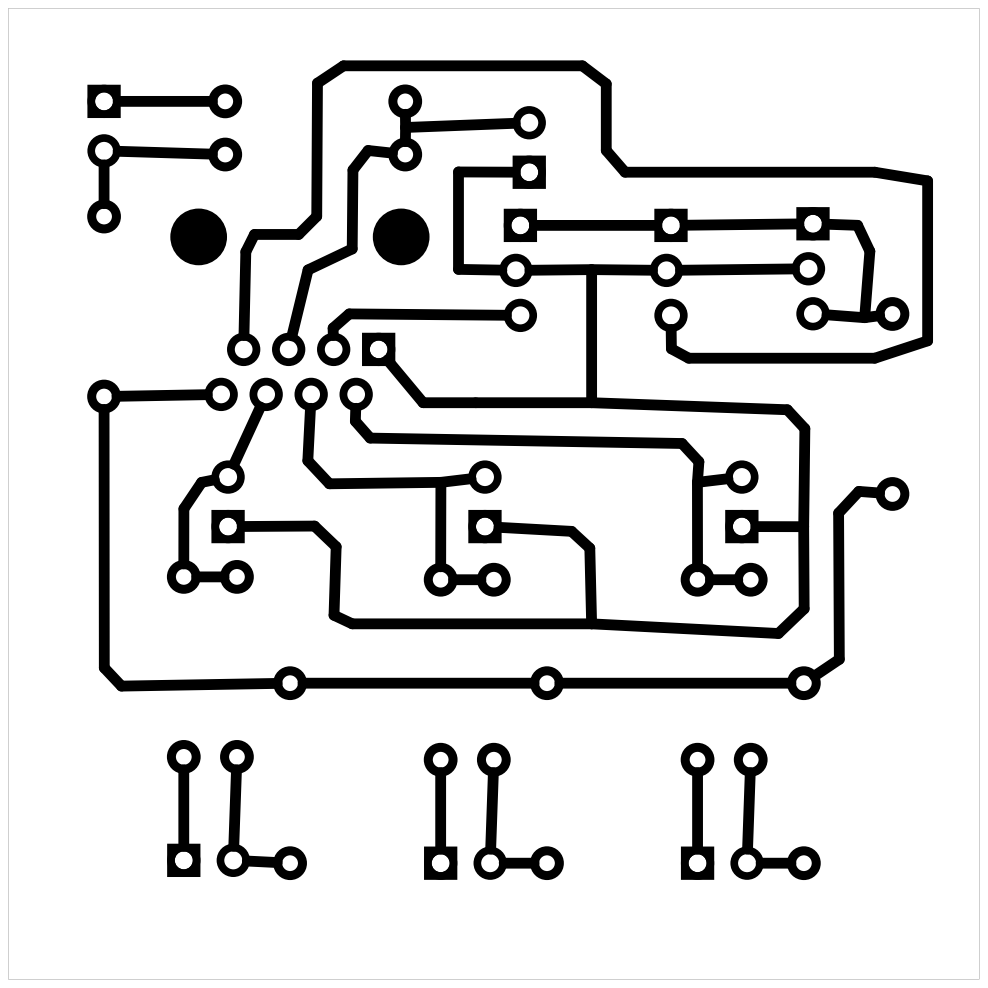
[picture p66: page 1]
