UnbDroid/balancer_race/placas/PDFs/sensores/sensores_etch_copper_bottom_mirror.pdf

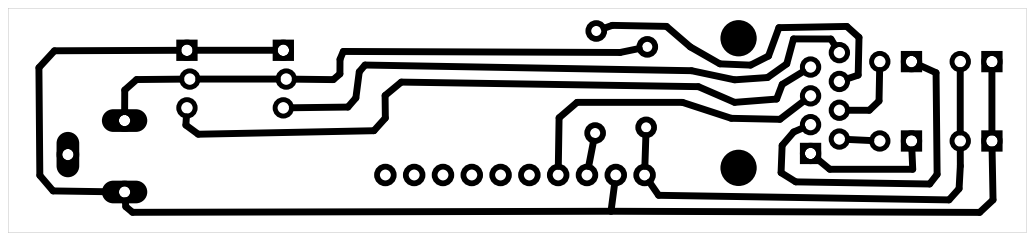
[picture p67: page 1]
