UnbDroid/balancer_race/placas/PDFs/alimentacao2/alimentacao2_etch_copper_bottom_mirror.pdf

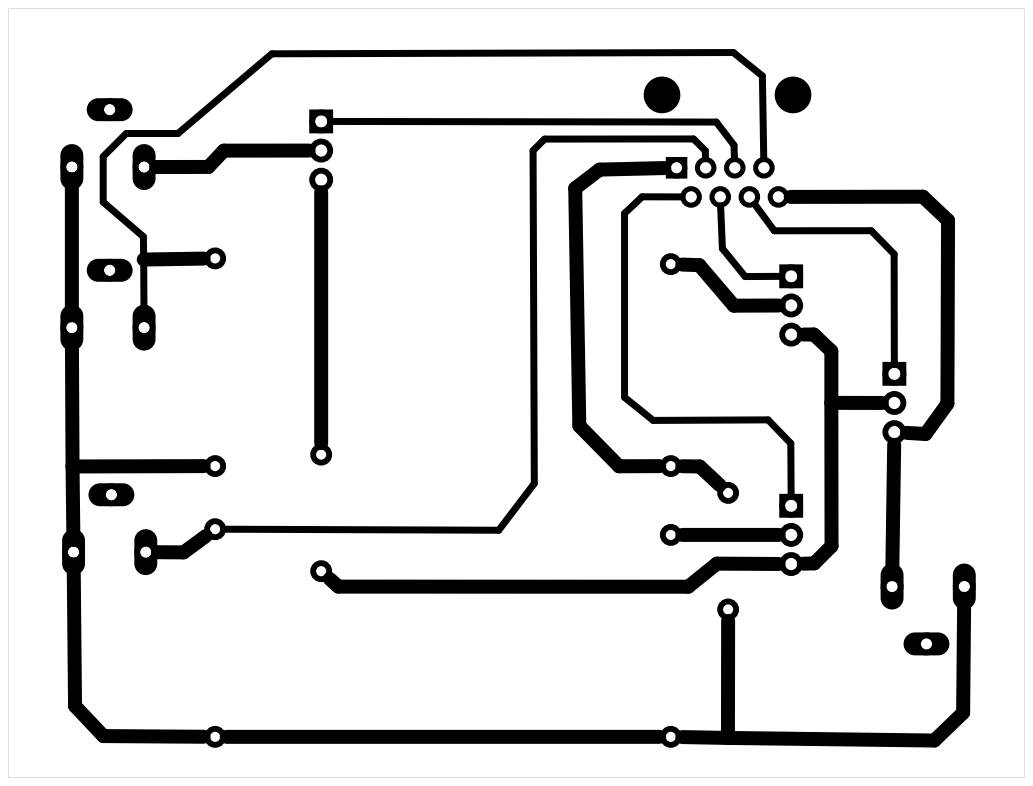
[picture p68: page 1]
