UnbDroid/balancer_race/code/watcher.c

#include <stdio.h>
#include <stdlib.h>
#include <wiringPi.h>
#include <unistd.h>
#include "jstick.c"
#include "led.c"

struct joystick js;
int keep_running = 1;
int led_finished = 1, joystick_finished = 1, watch_finished = 1;
int shutdown = 0, reboot = 0, close_program=0;
int debug_flag;

PI_THREAD(joystick)
{
    joystick_finished = 0;
	piHiPri(0);

    set_led_state(BLUETOOTH, ON);
    init_joystick(&js, devname);
    set_led_state(BLUETOOTH, OFF);

    while(!(js.select && js.start))
    {
        if(js.disconnect)
        {
        	set_led_state(BLUETOOTH, ON);
		    init_joystick(&js, devname);
		    set_led_state(BLUETOOTH, OFF);
		}
        update_joystick(&js);
	}
	if(js.dpad.down) shutdown = 1;
	if(js.dpad.up) reboot = 1;
	if(js.dpad.left) close_program = 1;
	keep_running = 0;
	joystick_finished = 1;
}

PI_THREAD(led)
{
	led_finished = 0;
	piHiPri(0);
	init_led();
	while(keep_running)
	{
		update_led();
		delay(50);
	}
	led_finished = 1;
}

int am_i_su()
{
    if(geteuid())
    	return 0;
    return 1;
}

void clean_up()
{
	set_color(RED, 255);
	light_rgb();
	while(!led_finished);
	set_color(RED, 255);
	light_rgb();
	while(!(joystick_finished));
	set_color(WHITE, 255);
	light_rgb();

	if(shutdown) system("sudo shutdown now&");
	else if(reboot) system("sudo shutdown -r now&");
	else if (!close_program) 
	{
		if(debug_flag) system("sudo /home/pi/ccdir/main -d&");
		else system("sudo /home/pi/ccdir/main&");
	}
}

int main(int argc, char* argv[])
{
	debug_flag = 0;
	if(argc > 1)
	{
		for(i = 1; i < argc; ++i)
		{
			if(	strcmp(argv[i], "-d") == 0 || strcmp(argv[i], "--debug") == 0 )
			{
				debug_flag = 1;
			}
		}
	}

	if(!am_i_su()) 
	{
		printf("Restricted area. Super users only.\n");
		return 0;
	}

	if(debug_flag)
	{
		printf("\e[2J\e[H");
		printf("  __       __             __                __                           \n |  \\  _  |  \\           |  \\              |  \\                          \n | $$ / \\ | $$  ______  _| $$_     _______ | $$____    ______    ______  \n | $$/  $\\| $$ |      \\|   $$ \\   /       \\| $$    \\  /      \\  /      \\ \n | $$  $$$\\ $$  \\$$$$$$\\\\$$$$$$  |  $$$$$$$| $$$$$$$\\|  $$$$$$\\|  $$$$$$\\\n | $$ $$\\$$\\$$ /      $$ | $$ __ | $$      | $$  | $$| $$    $$| $$   \\$$\n | $$$$  \\$$$$|  $$$$$$$ | $$|  \\| $$_____ | $$  | $$| $$$$$$$$| $$      \n | $$$    \\$$$ \\$$    $$  \\$$  $$ \\$$     \\| $$  | $$ \\$$     \\| $$      \n  \\$$      \\$$  \\$$$$$$$   \\$$$$   \\$$$$$$$ \\$$   \\$$  \\$$$$$$$ \\$$      \n  ");
	}

    wiringPiSetupPhys();
	piThreadCreate(joystick);
	piThreadCreate(led);
	set_led_state(STANDBY, ON);
	while(keep_running) delay(100);
	clean_up();

	return 0;
}
