UnbDroid/balancer_race/testes/writer.c

#include <fcntl.h>
#include <sys/stat.h>
#include <sys/types.h>
#include <unistd.h>

int main()
{
    int fd;
    char * myfifo = "/tmp/myfifo";

    /* create the FIFO (named pipe) */
    mkfifo(myfifo, 0666);

    /* write "Hi" to the FIFO */
    fd = open(myfifo, O_WRONLY);
    
    while(1)
    {
        write(fd, "ho", sizeof("ho"));
        sleep(0.5);
    }
    


    close(fd);

    /* remove the FIFO */
    unlink(myfifo);

    return 0;
}
